cartheur/aiventure-rodney/self-programming/trainer/circuit/CircuitDesc.md

# Creating a KiCad-Compatible JSON for the 8085 Trainer Schematic

The 8085 trainer kit with 62256 SRAM, 5 MHz clock, and SOD LED can be represented as a JSON schematic for KiCad, describing components and connections for the self-modifying code (program at `0000H`, I/O at `2000H`–`2001H`). While direct drawing isn’t possible, the JSON enables manual schematic entry or scripted import in KiCad.

## Approach
- **JSON**: Lists components (8085, 62256, etc.), pins, and nets.
- **KiCad**: Manually place components and connect nets in `eeschema`, or use a script for netlist import.
- **Assumptions**: Standard KiCad libraries (`device`, `74xx`, `microcontroller`), DIP footprints, no serial interface.
- **Limitations**: JSON is netlist-like, requiring manual placement or scripting for `.kicad_sch`.

## JSON Structure
Provided a JSON with:
- **Components**: 8085A, 62256, 74LS373, 74LS138, 5 MHz crystal, capacitors, resistors, LED, switches, 7805.
- **Nets**: VCC, GND, AD0–AD7, A0–A15, ALE, RD, WR, IO/M, CS_RAM, SOD, etc.
- **Notes**: Decoding, unused pins, KiCad import instructions.

## How to Use in KiCad
1. **Setup**: Install KiCad 7+, create project (`8085_trainer`).
2. **Add Components**: Place 8085A (DIP-40), 62256 (DIP-28), 74LS373, 74LS138, crystal, etc., from JSON.
3. **Connect Nets**: Wire per JSON (e.g., `AD0`: `U1.12` to `U3.3`, `U2.11`). Add VCC/GND power flags.
4. **Decoding**: 74LS138 Y0 to 62256 CS (`0000H`–`7FFFH`). G1 to IO/M, G2A/G2B to ground.
5. **Input**: DIP switch to 62256 D0–D7 for `2000H`.
6. **Annotate/Check**: Run `Annotate Schematic`, ERC.
7. **PCB**: Assign footprints, generate netlist, route in `pcbnew`.
8. **Manual Adjustments**: Use generic DIP-40 for 8085 if no symbol, add annotations.

## Loading JSON
- **Manual**: Place components, draw nets per JSON in `eeschema`.
- **Netlist**: Convert JSON to `.net` using Python (`skidl`, `kicad-netlist-utils`), import via `Tools > Import Netlist`.
- **Verify**: Check nets (e.g., `ALE`, `CS_RAM`), run ERC.

## Alternative: Manual Drawing
- **Components**: Place 8085, 62256, 74LS373, 74LS138, 5 MHz crystal, capacitors (22 pF, 10 µF, 0.1 µF, 100 µF), resistors (10 kΩ, 330Ω), LED, push-button, DIP switch, 7805.
- **Wiring**:
  - 8085: VCC, VSS, 5 MHz crystal, reset, SOD to LED.
  - 74LS373: Demultiplex AD0–AD7 to A0–A7.
  - 62256: A0–A14, D0–D7, CS, OE, WE.
  - 74LS138: A13–A15, IO/M, Y0 to CS.
  - DIP switch: To D0–D7.
  - 7805: 5V output, capacitors.
- **Save**: As `8085_trainer.kicad_sch`.

## Notes
- **JSON**: Netlist-like, lacks coordinates/UUIDs. Manual entry simplest.
- **Code**: Supports `0000H`, `2000H`–`2001H`, SOD LED.
- **62256**: A13–A14 grounded (8 KB) or decoded (32 KB).
- **5 MHz**: Compatible, no code changes.
- **KiCad**: Use global labels, group components, run ERC.

## Next Steps
- Enter schematic manually or script JSON to `.kicad_sch`.
- Export to PCB, build circuit.
- Test 62256, 5 MHz, SOD LED, `2001H` output.
- Document with PDF schematic, JSON, `selfmod.lst`.
