cartheur/aiventure-rodney/errata/Trainer-8085-schematic.odt

The circuit schematic for the 8085 trainer kit

Creating a schematic for the 8085 trainer kit with a 62256 SRAM, 5 MHz clock, and SOD LED indicator, as described, is feasible for visualization or implementation in KiCad. While I cannot directly draw a schematic (as I lack graphical output), I can provide a detailed JSON-like structure representing the schematic’s components, connections, and netlist, which you can import into KiCad to generate a schematic. This JSON will describe the 8085, 62256 SRAM, 74LS373 latch, 74LS138 decoder, 5 MHz clock circuit, reset circuit, SOD LED, DIP switch for input, and power supply, tailored to the self-modifying code’s requirements (program at 0000H, I/O at 2000H–2001H).

Approach

- JSON Structure: I’ll define a JSON object that includes:
  - Components (e.g., 8085, 62256, etc.) with part numbers, footprints, and pin assignments.
  - Nets (connections between pins, e.g., 8085 AD0–AD7 to 74LS373 D0–D7).
  - Annotations for KiCad compatibility (e.g., library references, net names).
- KiCad Import: You can use this JSON as a reference to manually create the schematic in KiCad or convert it to a KiCad schematic file (.kicad_sch) using a script (e.g., Python with kicad-netlist-utils) or a netlist import tool. KiCad’s native schematic format is complex, so the JSON will focus on a netlist-like structure that you can adapt.
- Assumptions:
  - Standard KiCad libraries (device, 74xx, microcontroller) are available.
  - Footprints assume DIP packages (e.g., DIP-40 for 8085, DIP-28 for 62256).
  - No serial interface (MAX232) is included to simplify the design, as the code can be loaded manually or via a monitor program.
- Limitations:
  - KiCad’s JSON import is not native for schematics; you’ll need to manually place components and route nets based on the JSON or use a netlist converter.
  - I’ll provide a simplified JSON for clarity, focusing on key connections. You may need to adjust for KiCad’s exact schema (e.g., UUIDs, coordinates).

JSON Schematic Representation

Below is a JSON-like structure describing the 8085 trainer kit’s schematic. It includes components, their pins, and net connections, organized to facilitate KiCad entry. The structure is inspired by netlist formats and KiCad’s schematic requirements.

See “circuit.json” in the repo.

How to Use the JSON in KiCad

1. Set Up KiCad:
  - Install KiCad (version 7 or later recommended).
  - Ensure standard libraries (device, 74xx, microcontroller, memory) are loaded.
  - Create a new project (e.g., 8085_trainer).
2. Create Schematic:
  - Open the Schematic Editor (eeschema).
  - Manually add components based on the JSON’s components section:
    - U1: 8085A (search for 8085 or use a generic DIP-40 microcontroller).
    - U2: HM62256 (use generic SRAM, DIP-28, e.g., 62256 in memory).
    - U3: 74LS373 (in 74xx library).
    - U4: 74LS138 (in 74xx).
    - Y1: Crystal (HC-49 in device).
    - C1–C5: Capacitors (C_0805 or C_1206 in device).
    - R1–R3: Resistors (R_0805 in device).
    - LED1: LED (LED_0805 in device).
    - SW1: Push-button switch (SW_Push in device).
    - SW2: 8-bit DIP switch (DIP-8 in device).
    - U5: 7805 (TO-220 in device).
  - Assign footprints as specified (e.g., DIP-40, DIP-28).
3. Connect Nets:
  - Use the JSON’s nets section to wire components:
    - Example: Net AD0 connects U1.12 (8085 AD0), U3.3 (74LS373 D0), U2.11 (62256 D0).
    - Use KiCad’s wire tool to draw connections.
    - Add labels (e.g., VCC, GND, AD0) for clarity.
  - Add power flags (PWR_FLAG in device) to VCC and GND nets to satisfy ERC (Electrical Rules Check).
  - Ground unused pins as noted (e.g., U1 SID, RST5.5, etc.).
4. Handle Decoding:
  - The 74LS138 selects the 62256 for 0000H–7FFFH (A15=0). Connect U4.6 (G1) to U1.34 (IO/M) directly or via a 74LS04 inverter if IO/M needs inversion.
  - Tie U4.4 (G2A) and U4.5 (G2B) to ground.
  - Connect U4.15 (Y0) to U2.20 (62256 CS).
5. Input Configuration:
  - The DIP switch (SW2) connects to the data bus (D0–D7) for input at 2000H. In KiCad, draw SW2 outputs to U2.11–U2.19 (62256 D0–D7).
  - For simplicity, the code assumes 2000H is RAM; no separate I/O chip is needed. If you want a dedicated input port, add a 74LS244 buffer enabled by a 74LS138 output (e.g., Y1 for 2000H).
6. Annotate and Check:
  - Run Annotate Schematic to assign unique references (e.g., U1, U2).
  - Run ERC to check for unconnected pins or net errors.
  - Manually verify nets against the JSON (e.g., AD0–AD7, A0–A14).
7. Export to PCB (Optional):
  - Assign footprints in eeschema.
  - Run Netlist Generation and import into pcbnew.
  - Place components and route traces for a physical board.
8. Manual Adjustments:
  - If KiCad lacks an 8085 symbol, use a generic DIP-40 microcontroller and label pins per the JSON.
  - Add text annotations in KiCad for clarity (e.g., “62256 CS for 0000H–7FFFH”).
  - If you want a native .kicad_sch file, use a Python script (e.g., kicad-netlist-utils) to convert the JSON to KiCad format, or manually draw based on the JSON.

Steps to Load JSON into KiCad

Since KiCad doesn’t directly import JSON schematics, follow these steps:

1. Manual Entry:
  - Open eeschema and place components listed in components (e.g., 8085A, HM62256).
  - Use the nets section to draw wires (e.g., connect U1.12 to U3.3 for AD0).
  - Label nets (e.g., VCC, GND, A0) for readability.
2. Netlist Conversion (Advanced):
  - Convert the JSON to a KiCad netlist (.net) using a Python script:
    - Parse components and nets to generate a netlist in KiCad’s format (e.g., (net VCC (node U1 40) (node U2 28) ...)).
    - Libraries like skidl or kicad-netlist-utils can help.
  - Import the netlist into eeschema via Tools > Import Netlist.
  - Manually place components, as netlists don’t include coordinates.
3. Verify:
  - Check connections against the JSON (e.g., ALE from U1.30 to U3.11).
  - Run ERC to ensure no floating pins or duplicate nets.
  - Add power flags for VCC and GND.

Alternative: Drawing the Schematic

If you prefer to draw the schematic directly in KiCad without JSON:

1. Add Components:
  - Place the 8085 (DIP-40), 62256 (DIP-28), 74LS373 (DIP-20), 74LS138 (DIP-16), 5 MHz crystal, capacitors (22 pF, 10 µF, 0.1 µF, 100 µF), resistors (10 kΩ, 330Ω), LED, push-button, DIP switch, and 7805.
2. Wire Connections:
  - 8085:
    - Vcc (pin 40), Vss (pin 20), 0.1 µF capacitor.
    - 5 MHz crystal to X1/X2 (pins 1–2), 22 pF capacitors to ground.
    - Reset: 10 µF to 5V, 10 kΩ to ground, push-button across capacitor at RESET_IN (pin 36).
    - SOD (pin 4) to 330Ω resistor, to LED cathode, anode to 5V.
    - Ground TRAP (pin 6) via 10 kΩ.
  - 74LS373:
    - D0–D7 (pins 3, 4, 7, 8, 13, 14, 17, 18) to 8085 AD0–AD7 (pins 12–19).
    - Q0–Q7 (pins 2, 5, 6, 9, 12, 15, 16, 19) to 62256 A0–A7 (pins 10, 9, 8, 7, 6, 5, 4, 3).
    - G (pin 11) to 8085 ALE (pin 30), OC (pin 1) to ground.
  - 62256:
    - A0–A12 (pins 10, 9, 8, 7, 6, 5, 4, 3, 25, 24, 21, 23, 2) to A0–A12 (A0–A7 from 74LS373, A8–A12 from 8085 pins 21–25).
    - A13–A14 (pins 26, 1) to 8085 A13–A14 (pins 26–27) or ground for 8 KB.
    - D0–D7 (pins 11–13, 15–19) to 8085 AD0–AD7.
    - CS (pin 20) to 74LS138 Y0 (pin 15).
    - OE (pin 22) to 8085 RD (pin 32), WE (pin 27) to WR (pin 31).
  - 74LS138:
    - A, B, C (pins 1–3) to 8085 A13–A15 (pins 26–28).
    - G1 (pin 6) to 8085 IO/M (pin 34), G2A/G2B (pins 4–5) to ground.
    - Y0 (pin 15) to 62256 CS.
  - DIP Switch:
    - Outputs (D0–D7) to 62256 D0–D7 (pins 11–13, 15–19) via 10 kΩ pull-ups to 5V.
    - Enable via 74LS138 Y1 (pin 14) for 2000H read (optional; code uses RAM).
  - Power:
    - 7805 VOUT (pin 3) to VCC net, VIN (pin 1) to 9–12V, GND (pin 2).
    - 100 µF, 0.1 µF capacitors at 7805 input/output.
3. Annotate and Save:
  - Run Annotate Schematic.
  - Save as 8085_trainer.kicad_sch.

Notes

- JSON Limitations:
  - The JSON is a netlist-like representation, not a native KiCad .kicad_sch file. It lacks graphical coordinates and UUIDs, requiring manual placement in KiCad.
  - For a true .kicad_sch, you’d need a Python script to generate KiCad’s S-expression format, which is complex and beyond this scope.
- Simplifications:
  - The DIP switch is connected directly to the data bus, assuming 2000H input is set via RAM writes or manual monitor entry. A proper I/O port (e.g., 74LS244) would need additional decoding.
  - No EPROM or serial interface is included to keep the schematic minimal. Add a 2764 or MAX232 if needed.
- KiCad Tips:
  - Use global labels (e.g., VCC, GND) to reduce clutter.
  - Group components logically (e.g., 8085 near 74LS373, 62256 near 74LS138).
  - Save frequently and run ERC to catch errors.
- Code Compatibility:
  - The schematic supports the code’s requirements: program at 0000H, I/O at 2000H–2001H, SOD LED for self-modification.
  - The 62256’s 32 KB covers all addresses; grounding A13–A14 simplifies decoding to 8 KB if preferred.
  - The 5 MHz clock (2.5 MHz internal) is compatible, with no code changes needed.

Next Steps

1. Manual KiCad Entry:
  - Use the JSON as a reference to place components and draw nets in eeschema.
  - Start with the 8085, add 74LS373 for demultiplexing, then 62256 and 74LS138.
  - Add clock, reset, LED, and DIP switch last.
2. Scripted Import (Optional):
  - Write a Python script to convert the JSON to a KiCad netlist or .kicad_sch file.
  - Example libraries: skidl for schematic generation, kicad-python for KiCad file manipulation.
3. PCB Design:
  - After completing the schematic, generate a netlist and import into pcbnew for PCB layout.
  - Use DIP sockets for easy IC replacement.
4. Build and Test:
  - Assemble the circuit on a breadboard or PCB based on the KiCad schematic.
  - Test as described (5 MHz clock, 62256 access, SOD LED, 2001H output).
5. Documentation:
  - Export the KiCad schematic as a PDF for reference.
  - Keep the JSON and selfmod.lst for debugging.
