cartheur/aiventure-rodney/diagrams/RodneyWirewrapStack.pdf

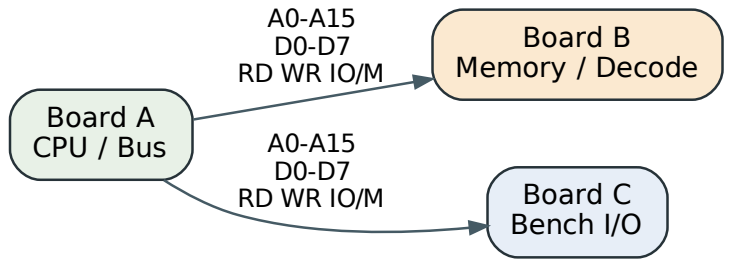
[picture p6: figure]
Board A CPU / Bus; Board B Memory / Decode; Board C Bench I/O
