cartheur/aiventure-rodney/book/figures/Figure-04_1.jpg

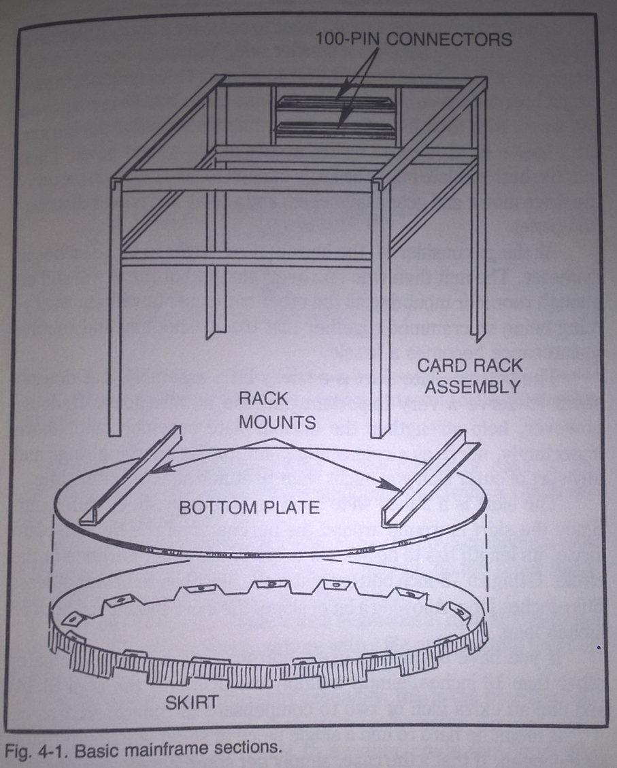
book/figures/Figure-04_1.jpg
