cartheur/aiventure-rodney/book/figures/Figure-04_2.jpg

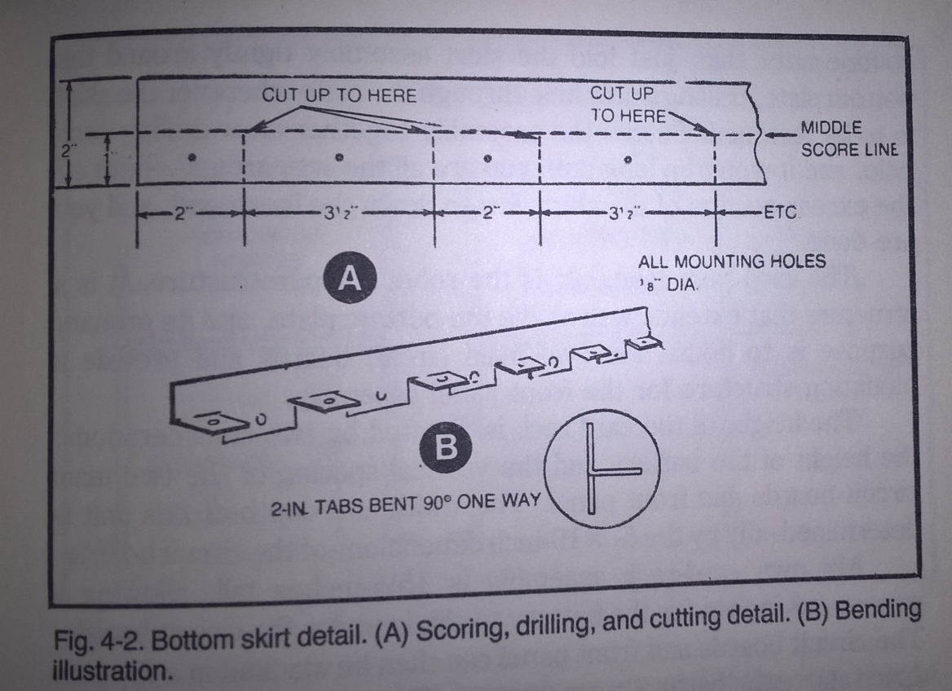
book/figures/Figure-04_2.jpg
