cartheur/aiventure-rodney/book/figures/Figure-04_3.jpg

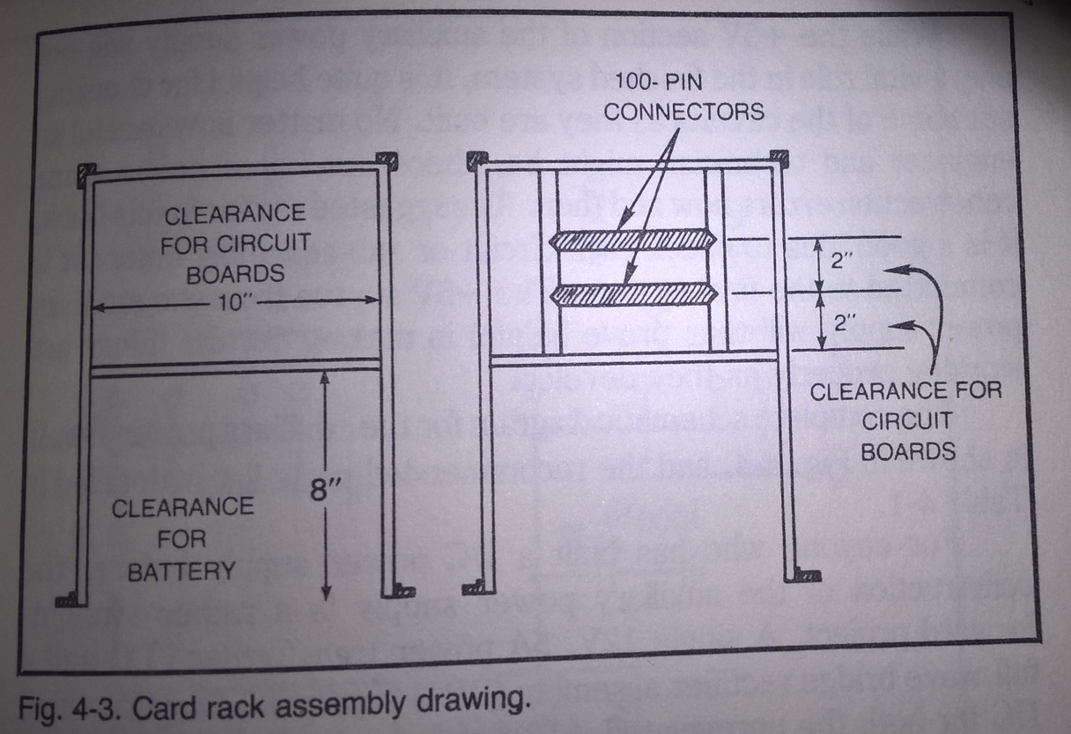
book/figures/Figure-04_3.jpg
