cartheur/aiventure-rodney/book/figures/Figure-04_5.jpg

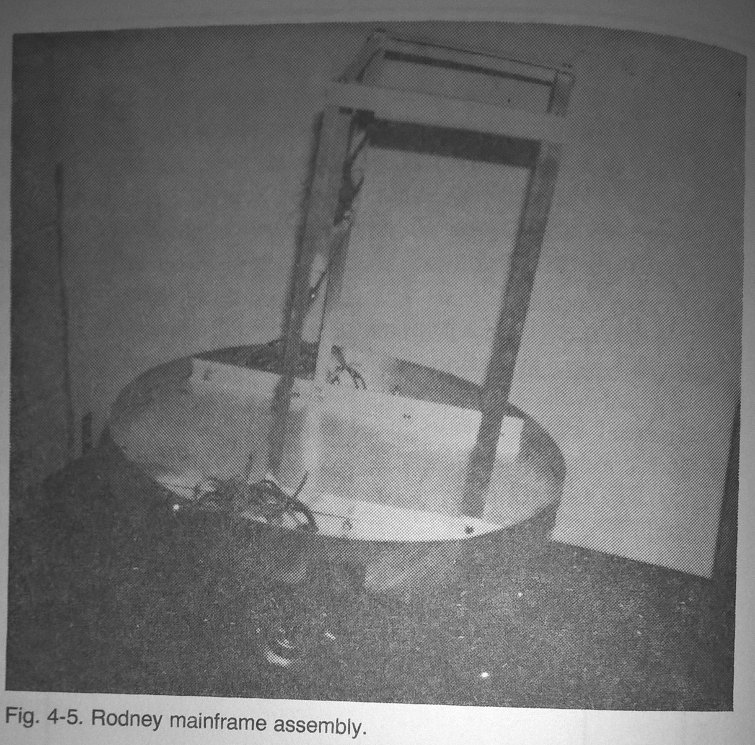
book/figures/Figure-04_5.jpg
