cartheur/aiventure-rodney/book/figures/Figure-05_12.jpg

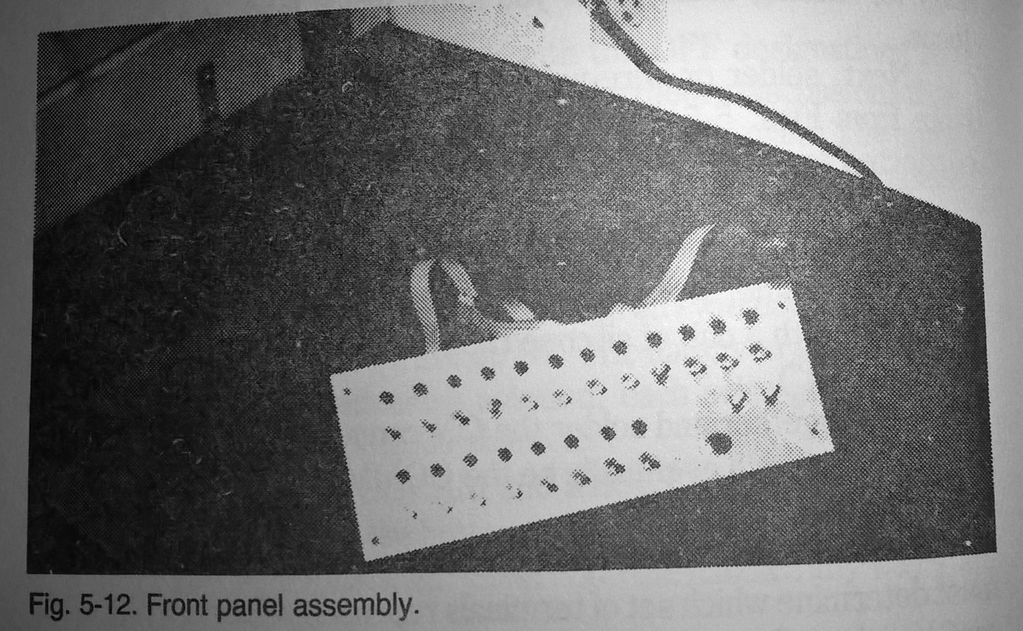
book/figures/Figure-05_12.jpg
