cartheur/aiventure-rodney/book/figures/Figure-06_7.jpg

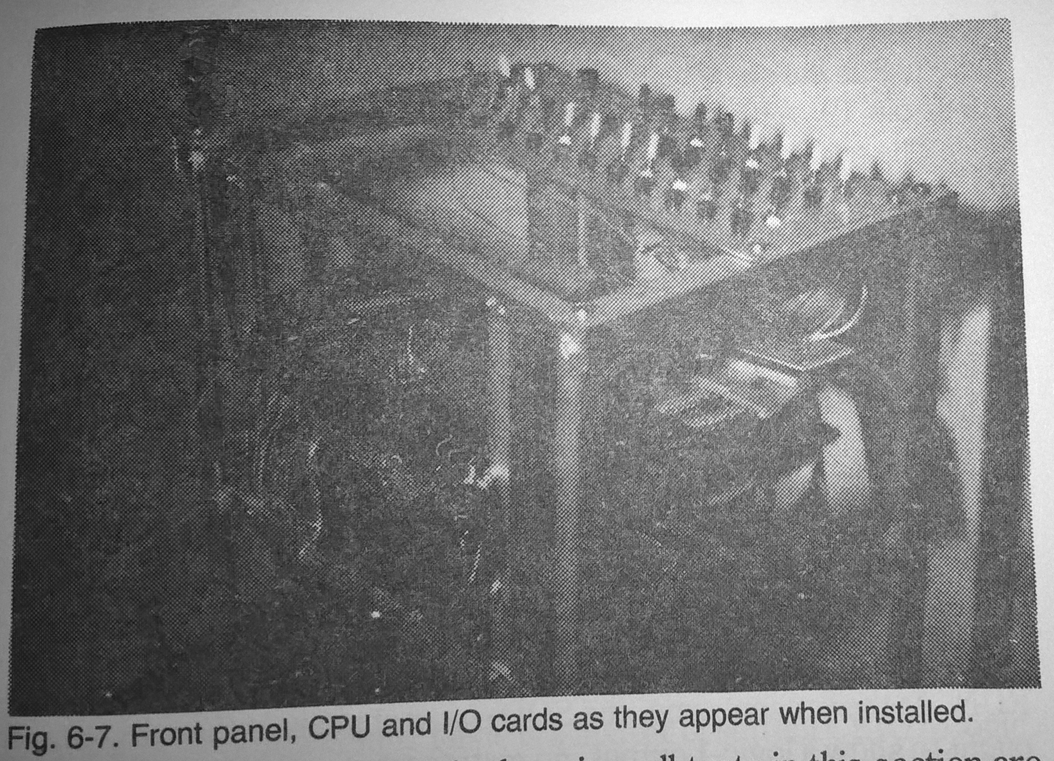
book/figures/Figure-06_7.jpg
