cartheur/aiventure-rodney/book/figures/Figure-07_9.jpg

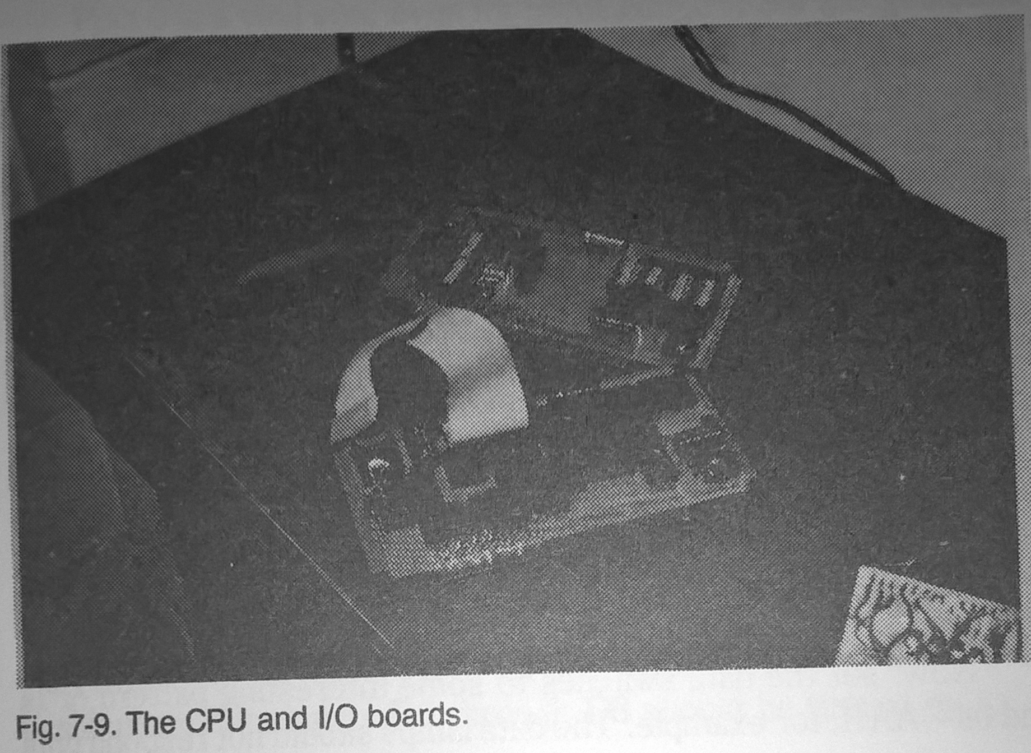
book/figures/Figure-07_9.jpg
