cartheur/aiventure-rodney/book/figures/Figure-08_8.jpg

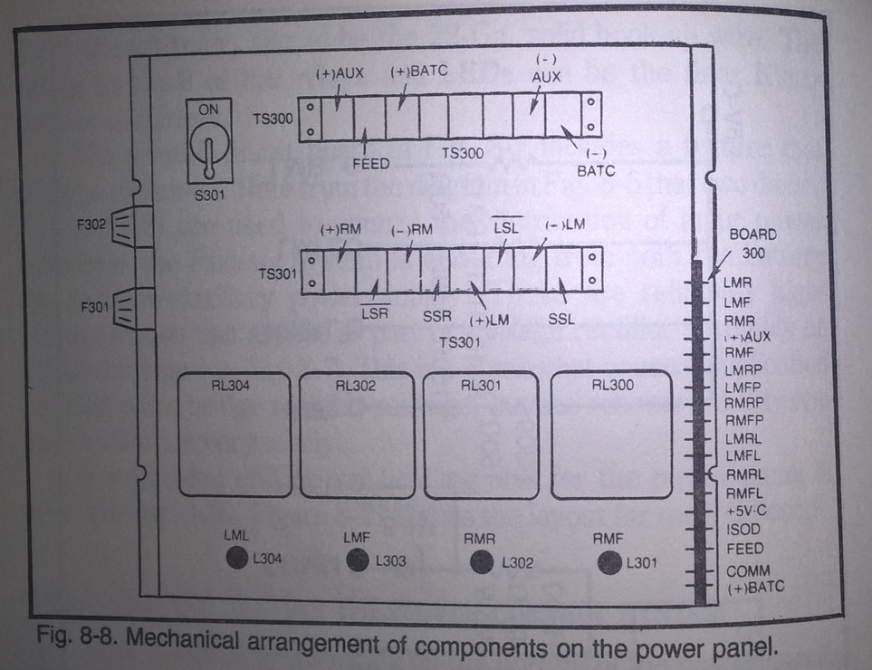
book/figures/Figure-08_8.jpg
