cartheur/aiventure-rodney/book/figures/Figure-08_9.jpg

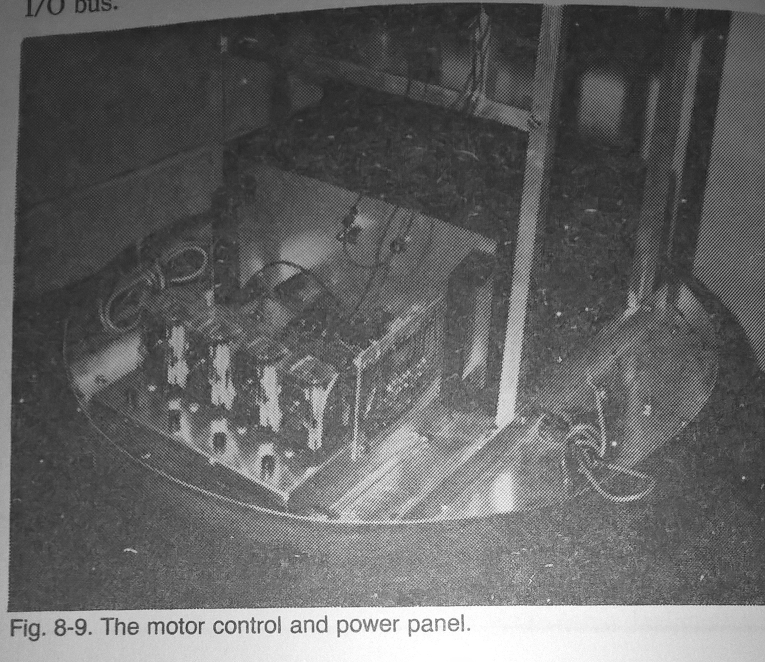
book/figures/Figure-08_9.jpg
