cartheur/aiventure-rodney/book/figures/Figure-08_10.jpg

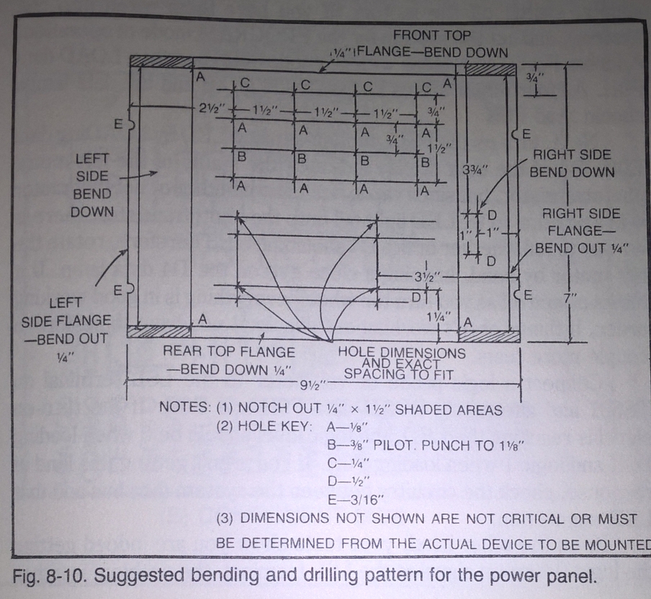
book/figures/Figure-08_10.jpg
