cartheur/aiventure-rodney/book/figures/Figure-08_12.jpg

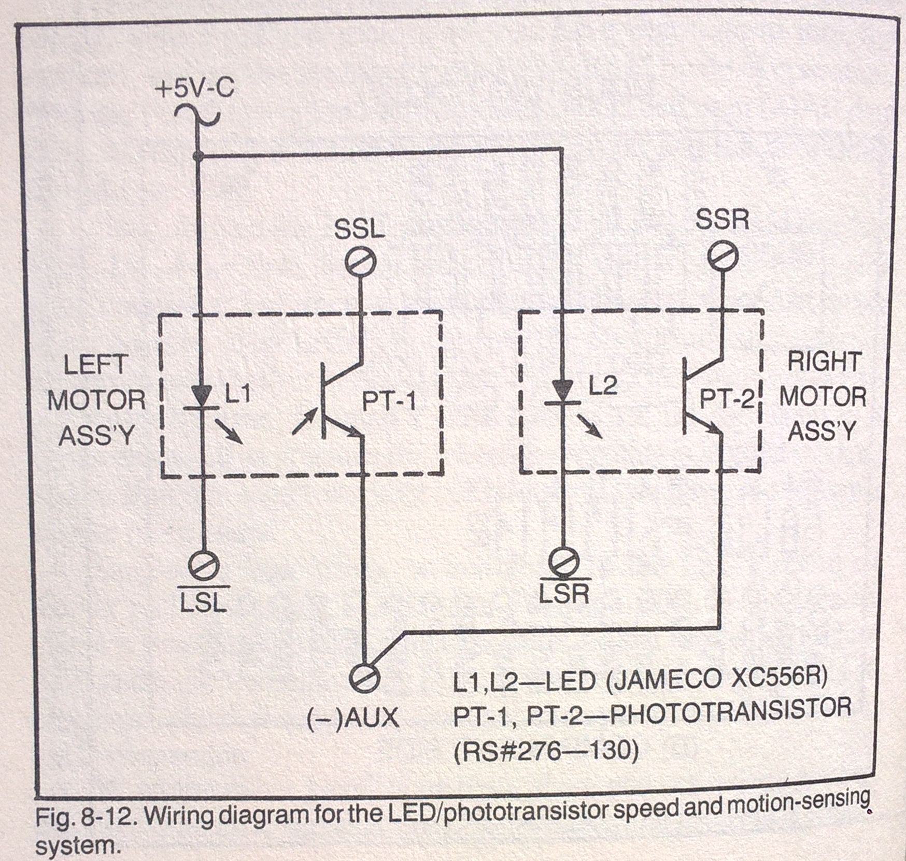
book/figures/Figure-08_12.jpg
