cartheur/aiventure-rodney/book/figures/Figure-08_13.jpg

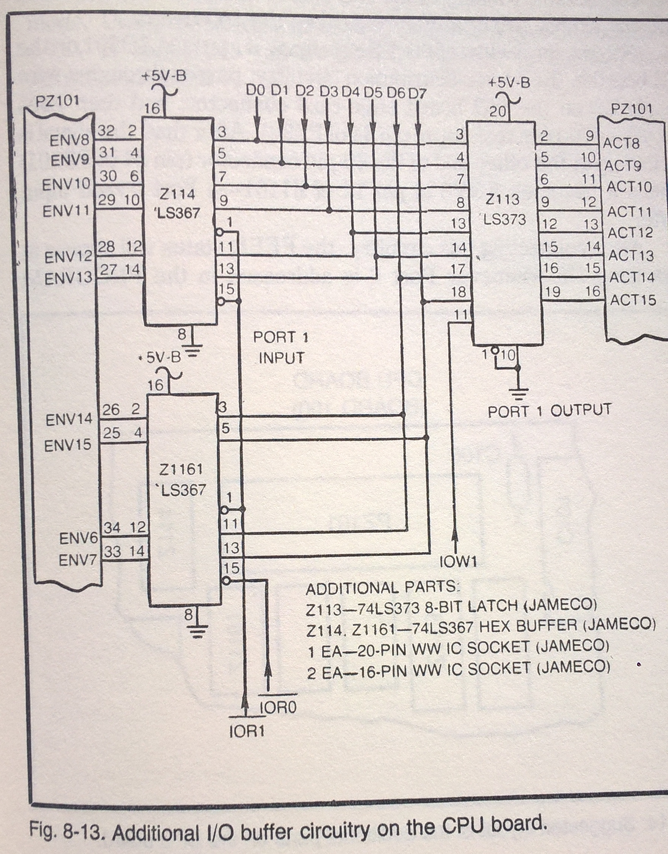
book/figures/Figure-08_13.jpg
