cartheur/aiventure-rodney/book/figures/Figure-09_5.jpg

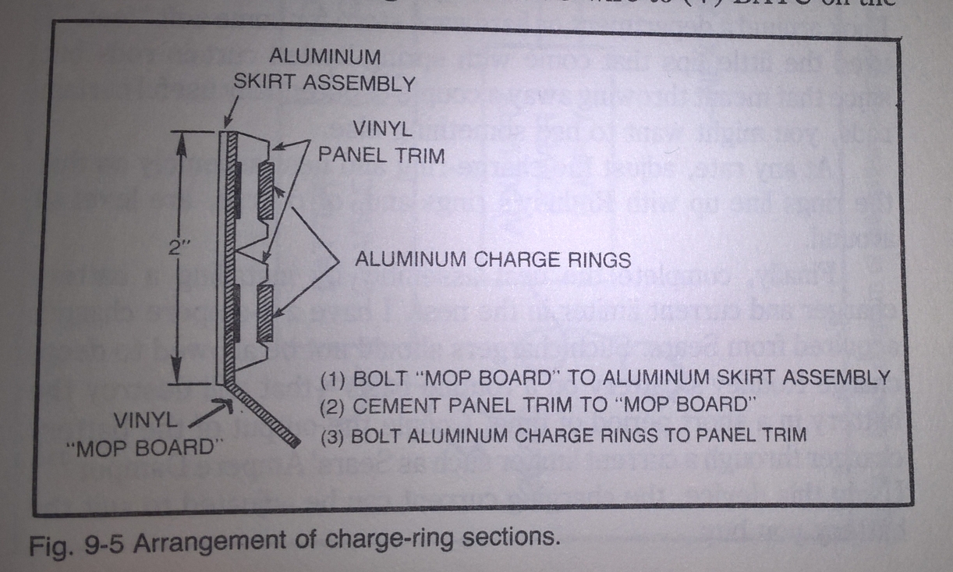
book/figures/Figure-09_5.jpg
