cartheur/aiventure-rodney/book/finished/Rodney-Heiserman-1979-p1a-x640.jpg

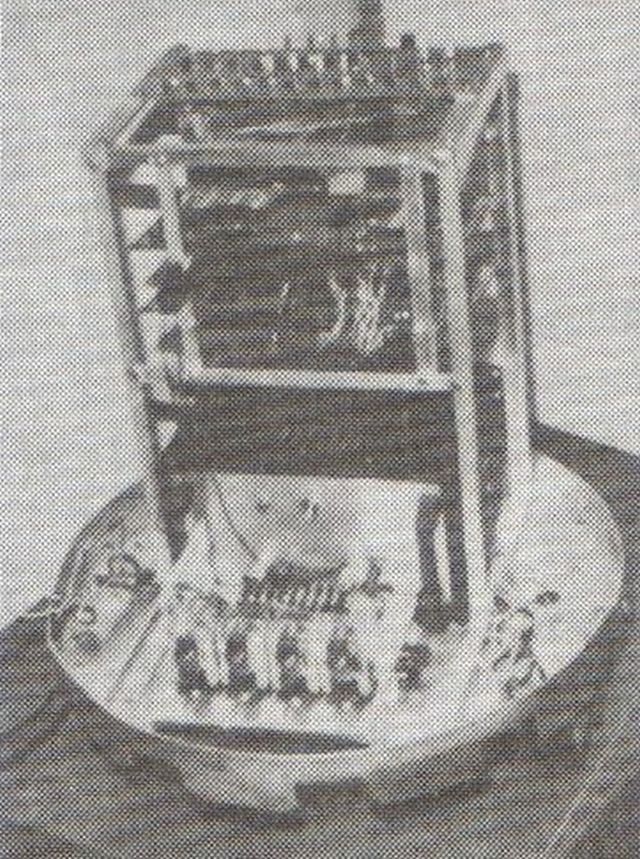
book/finished/Rodney-Heiserman-1979-p1a-x640.jpg
