cartheur/aiventure-rodney/book/finished/Rodney-Heiserman-1979-p1b-x640.jpg

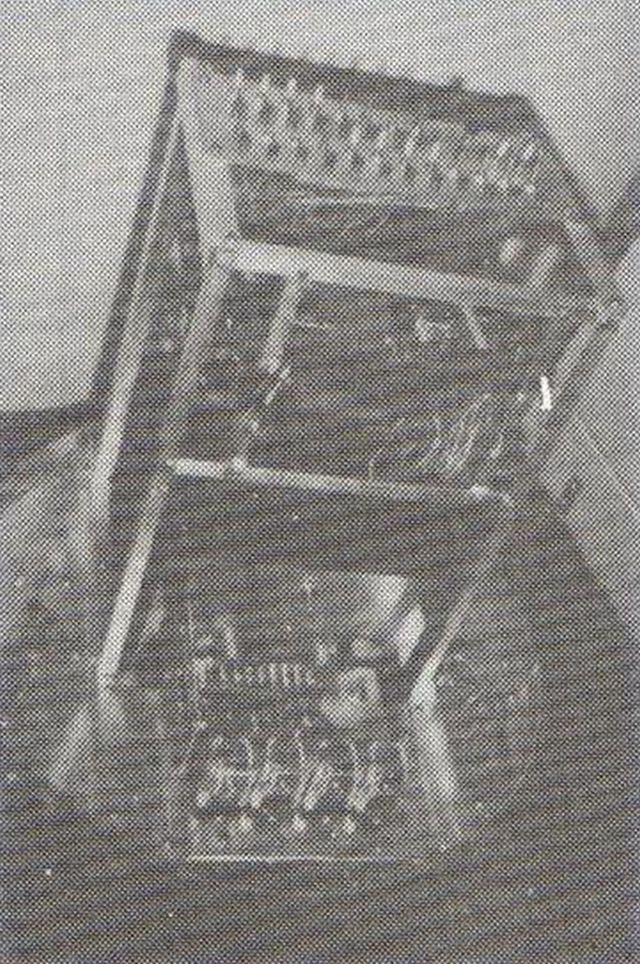
book/finished/Rodney-Heiserman-1979-p1b-x640.jpg
