cartheur/aiventure-rodney/book/finished/Rodney-Heiserman-1979-p2-x640.jpg

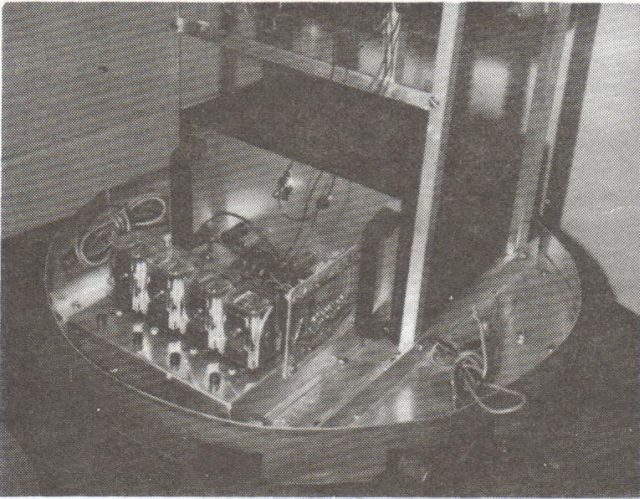
book/finished/Rodney-Heiserman-1979-p2-x640.jpg
