cartheur/aiventure-rodney/book/programming/3.jpg

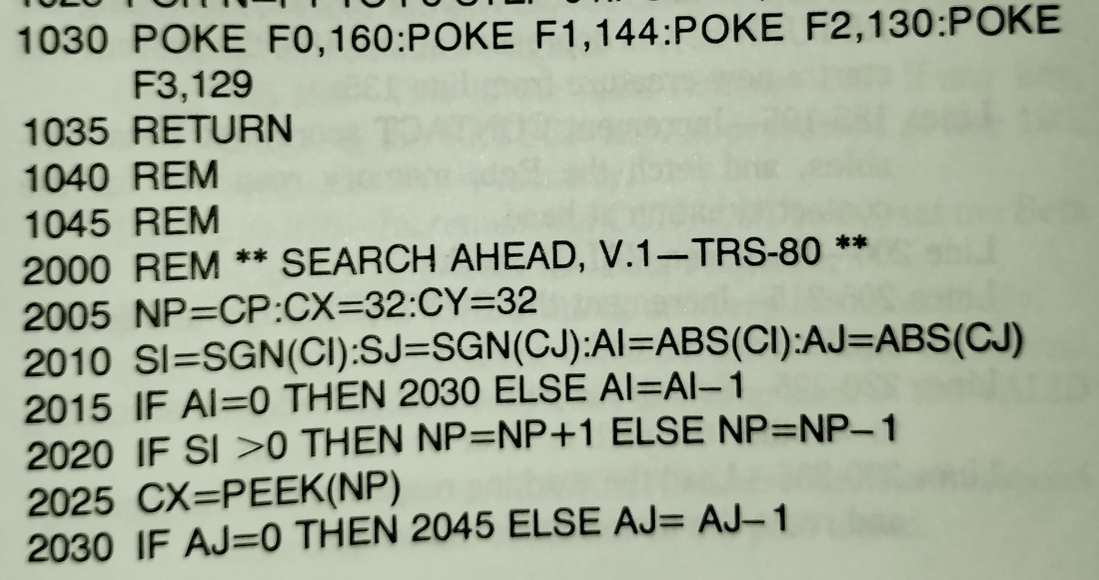
book/programming/3.jpg
