cartheur/aiventure-rodney/book/programming/fig.19-3.jpg

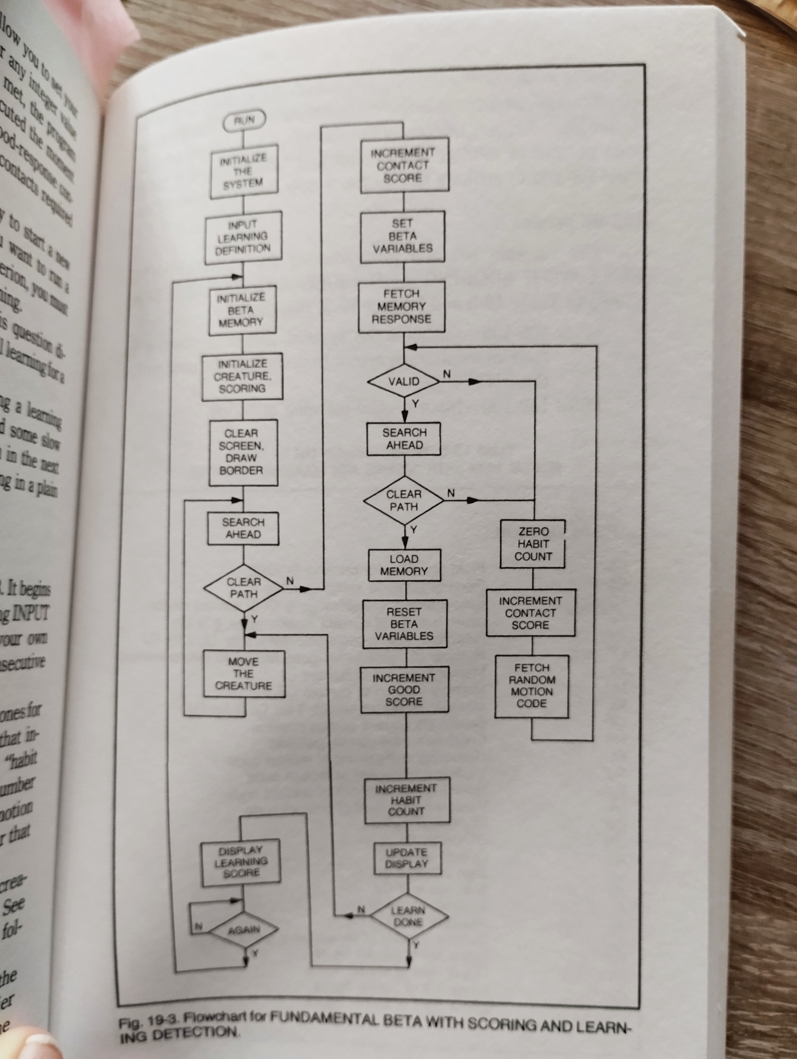
book/programming/fig.19-3.jpg
