cartheur/aiventure-rodney/book/programming/fig.19.2.jpg

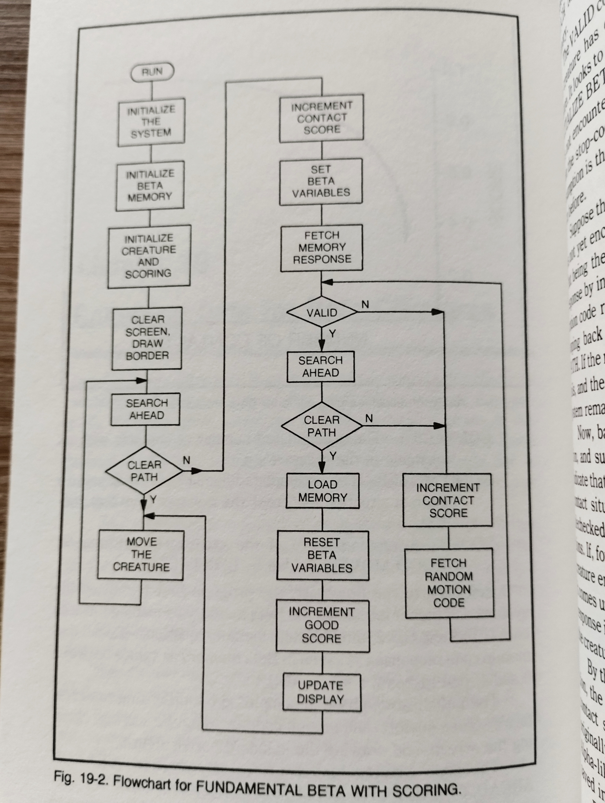
book/programming/fig.19.2.jpg
