cartheur/aiventure-rodney/book/programming/p272.jpg

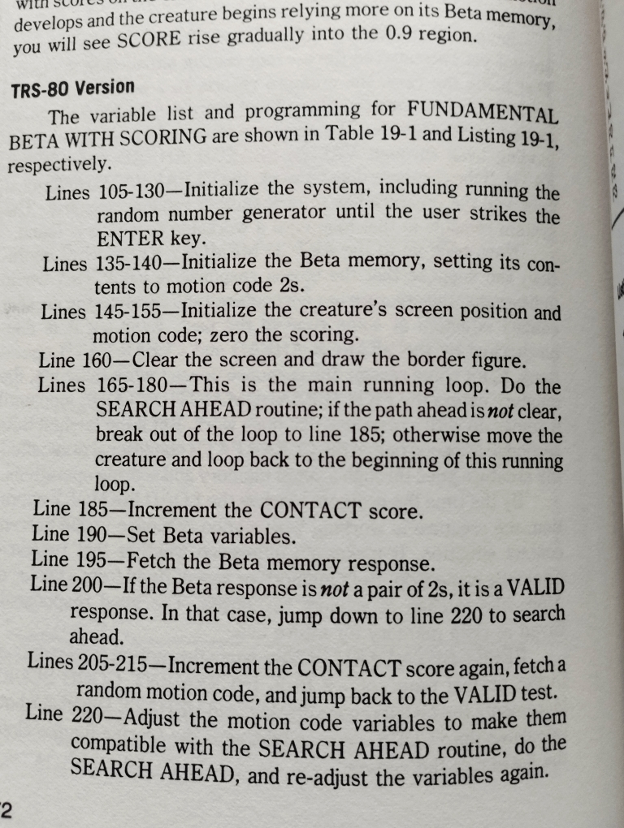
book/programming/p272.jpg
