cartheur/aiventure-rodney/book/tables/Table-04_1.jpg

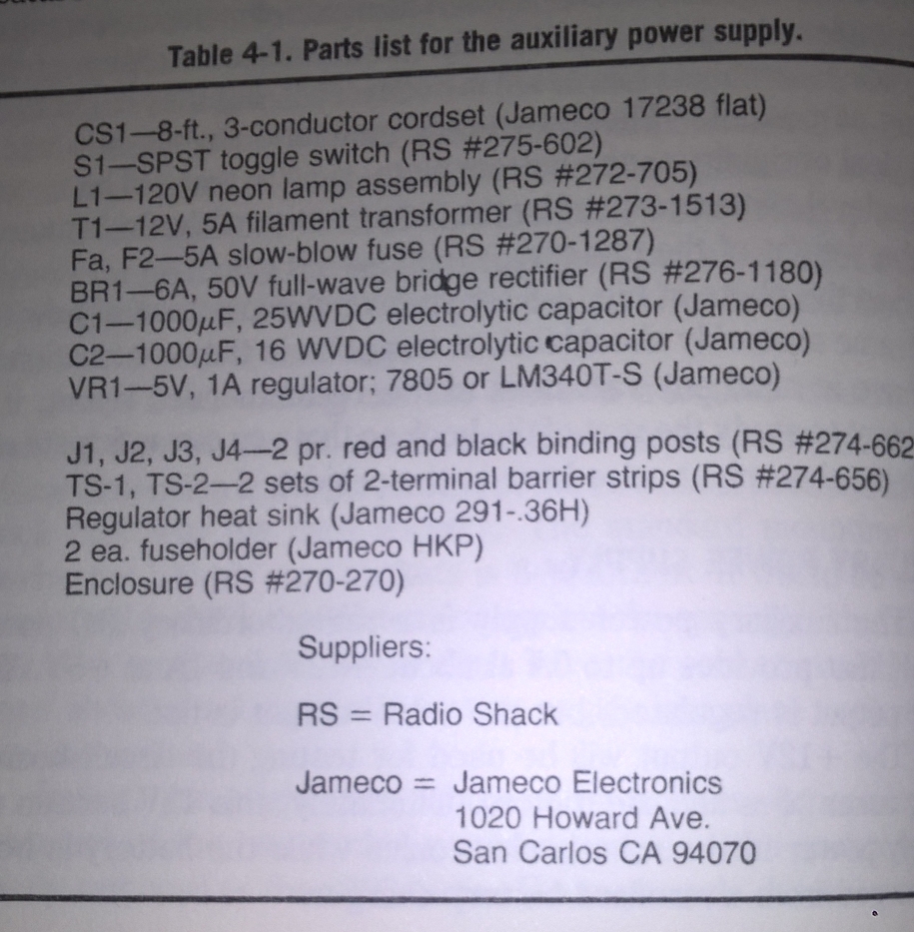
book/tables/Table-04_1.jpg
