cartheur/aiventure-rodney/book/tables/Table-05_1.jpg

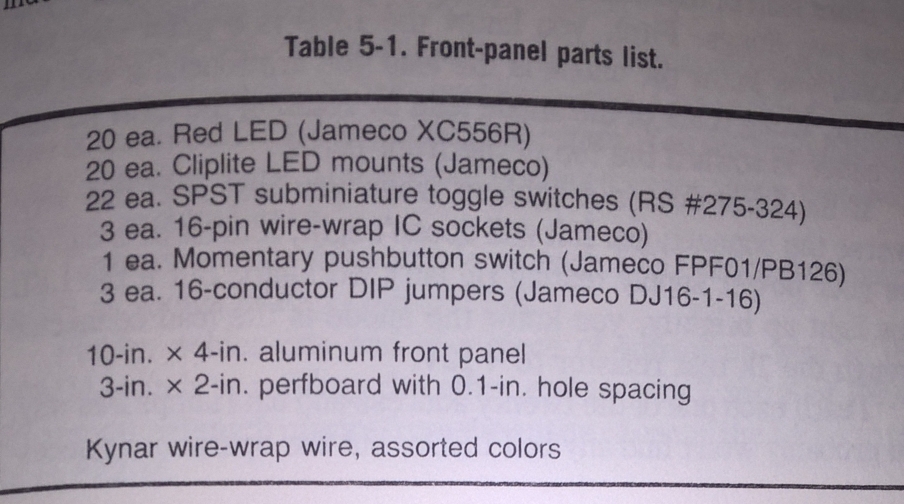
book/tables/Table-05_1.jpg
