cartheur/aiventure-rodney/book/tables/Table-05_2.jpg

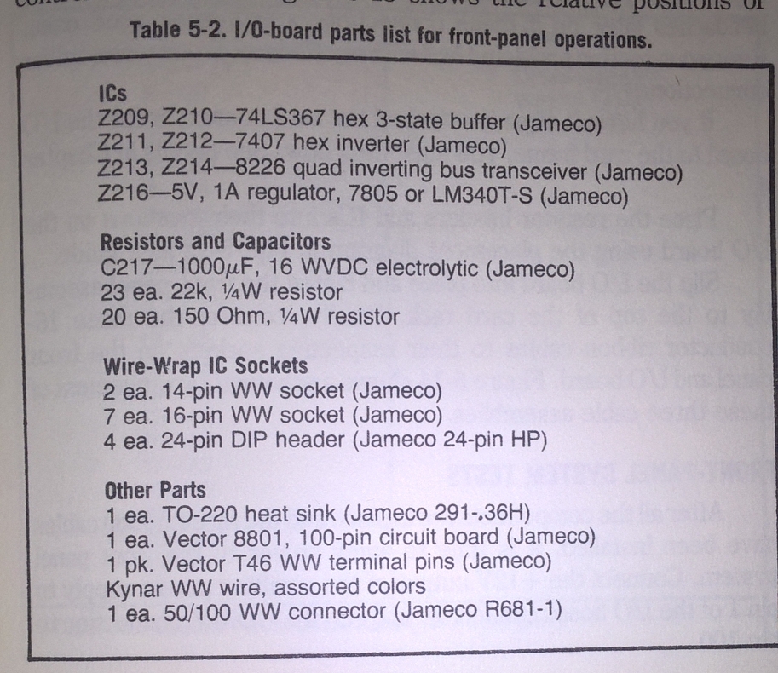
book/tables/Table-05_2.jpg
