cartheur/aiventure-rodney/book/tables/Table-06_3.jpg

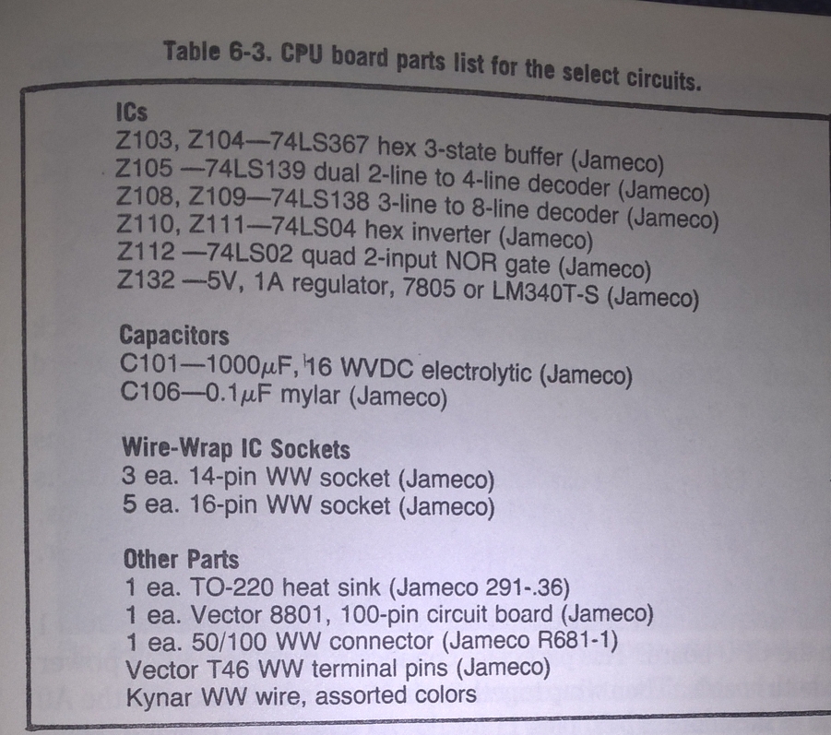
book/tables/Table-06_3.jpg
