cartheur/aiventure-rodney/book/tables/Table-07_2.jpg

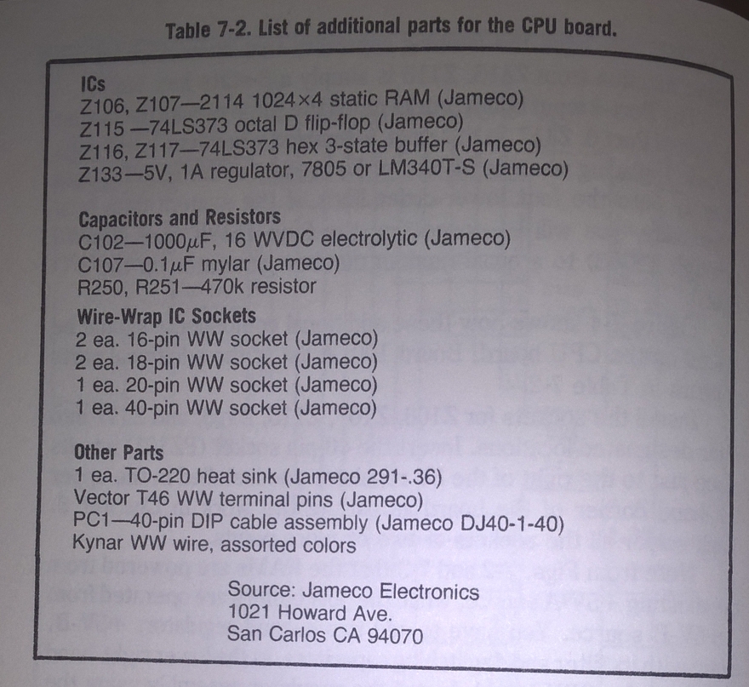
book/tables/Table-07_2.jpg
