cartheur/aiventure-rodney/book/tables/Table-08_2.jpg

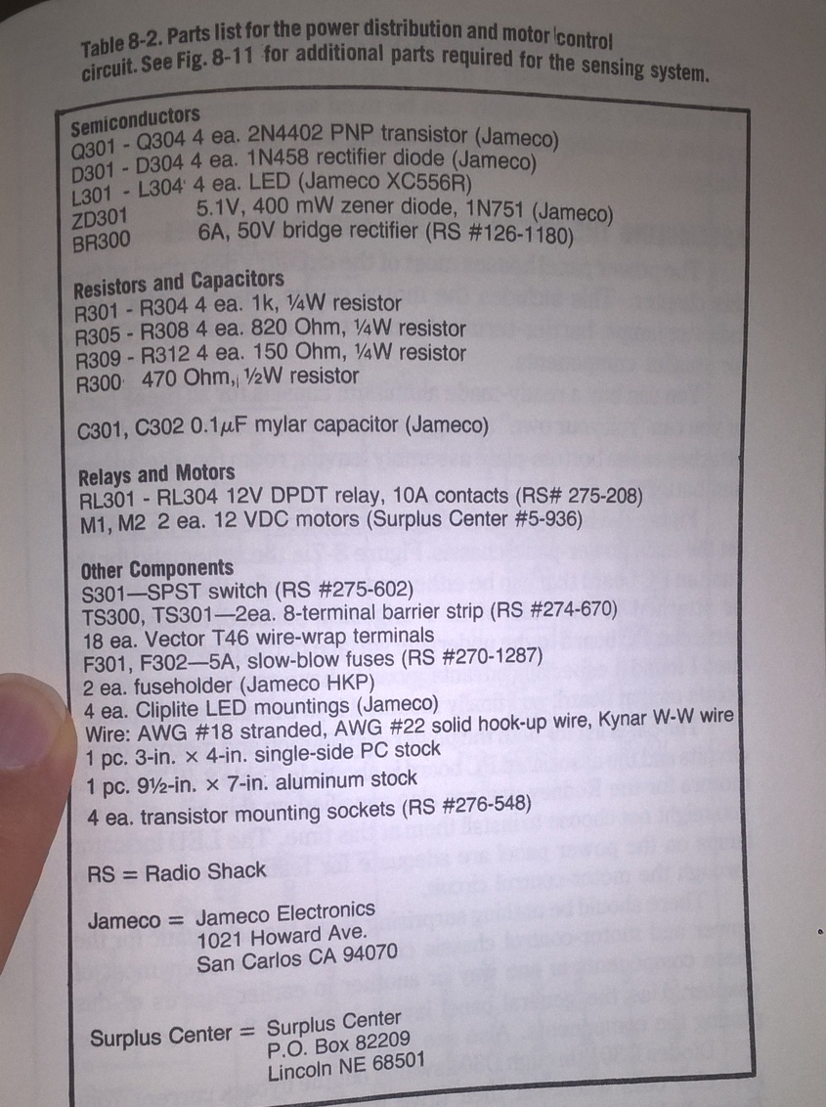
book/tables/Table-08_2.jpg
