cartheur/aiventure-rodney/book/tables/Table-09_1.jpg

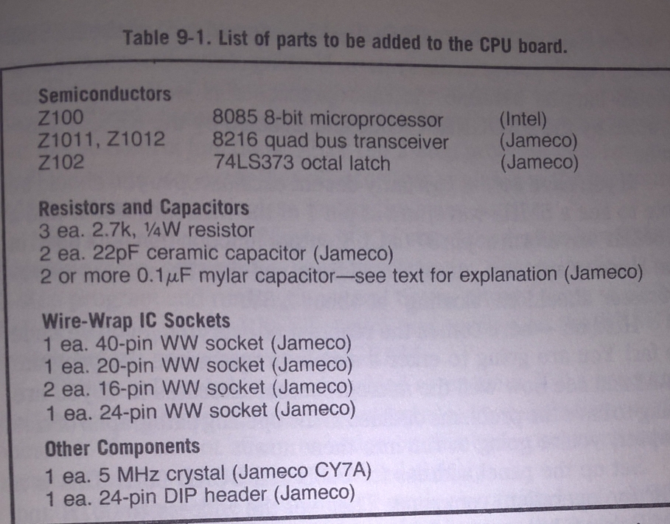
book/tables/Table-09_1.jpg
