cartheur/aiventure-rodney/book/tables/Table-09_2.jpg

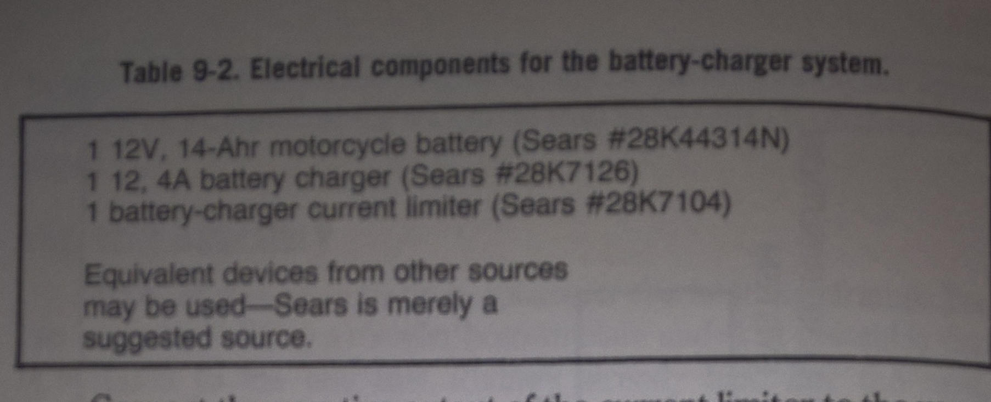
book/tables/Table-09_2.jpg
