cartheur/aiventure-rodney/book/tables/Table-11_1.jpg

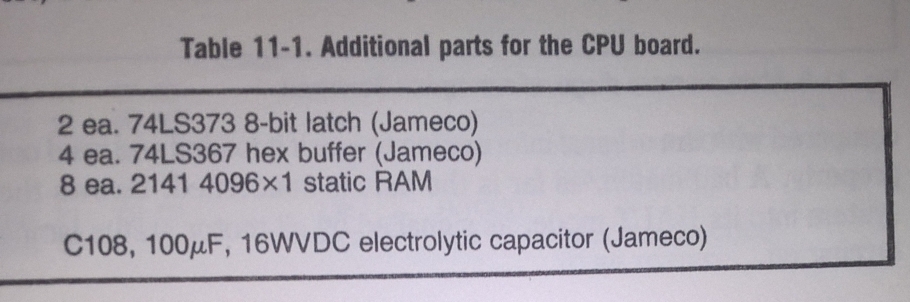
book/tables/Table-11_1.jpg
