cartheur/aiventure-rodney/build-of-materials/datasheets/vector/8801-6-specs.png

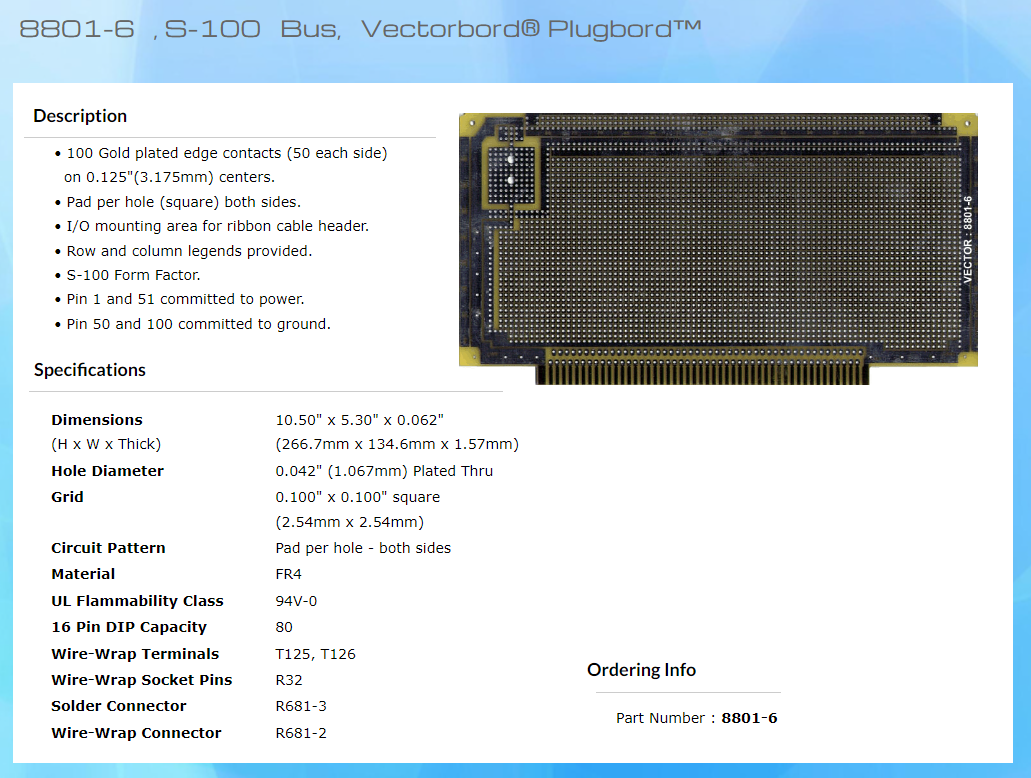
build-of-materials/datasheets/vector/8801-6-specs.png
