cartheur/aiventure-rodney/build/5-front-panel/images/panel_design.png

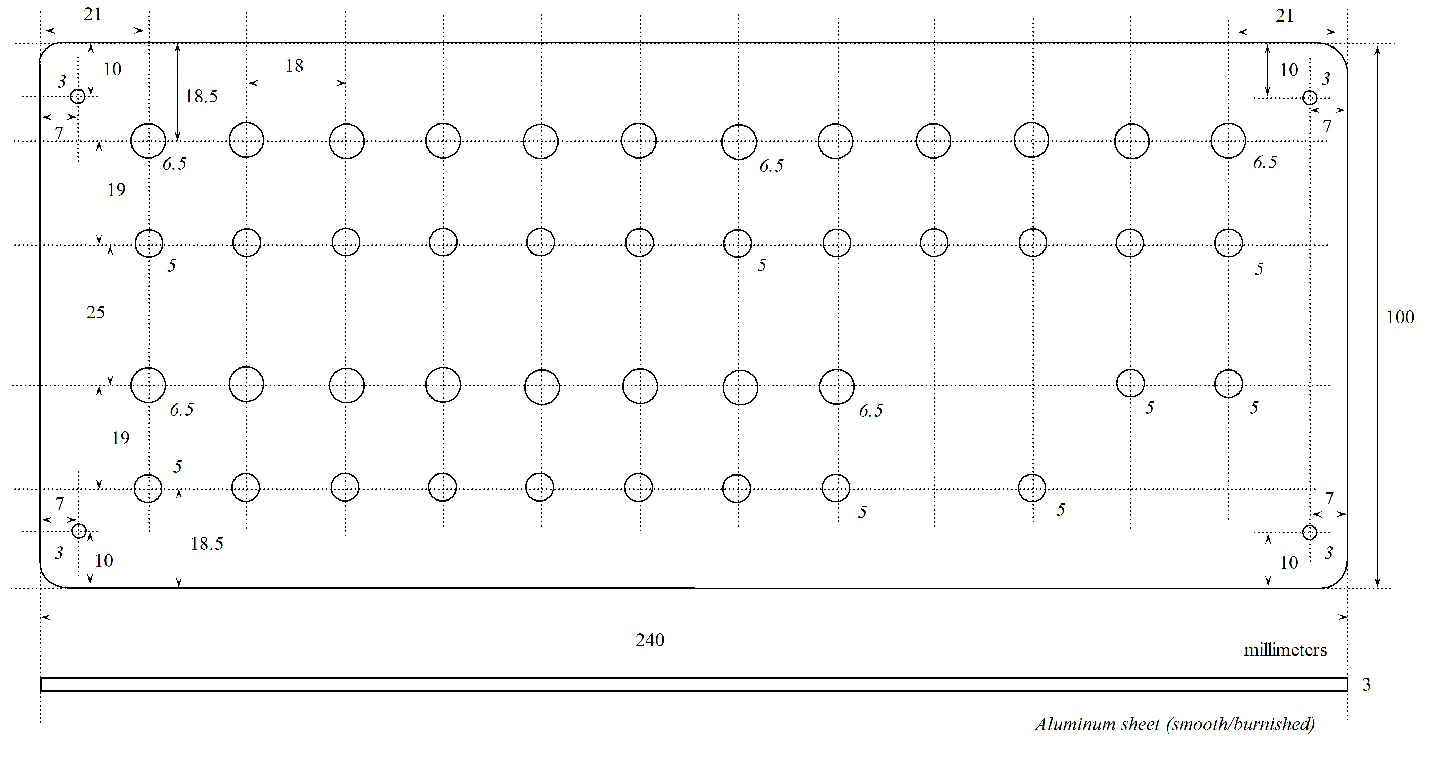
build/5-front-panel/images/panel_design.png
