cartheur/aiventure-rodney/design/rodney-bw.jpg

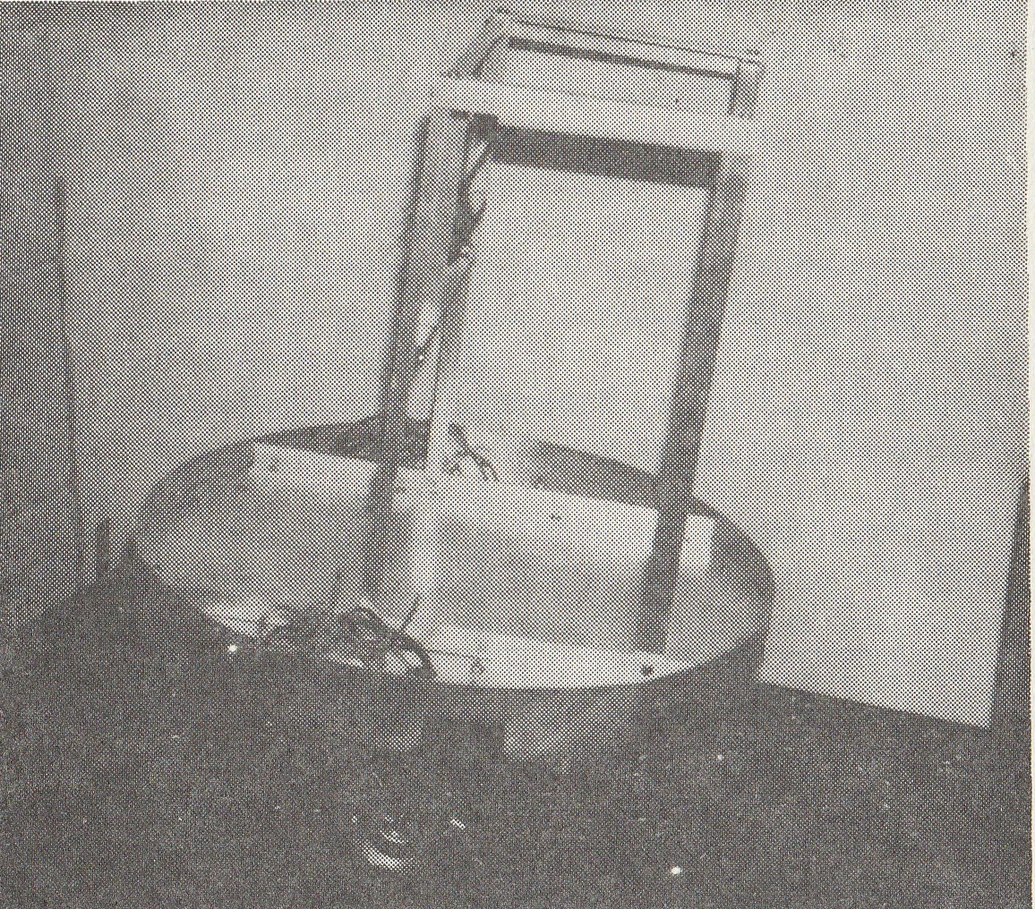
design/rodney-bw.jpg
