cartheur/aiventure-rodney/design/rodney-color.jpg

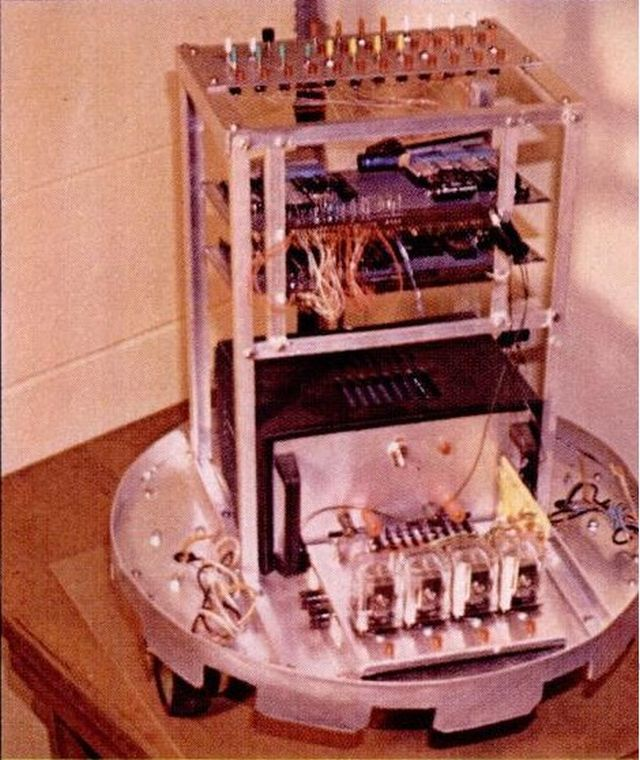
design/rodney-color.jpg
