cartheur/aiventure-rodney/development/prototype/major-tom.jpg

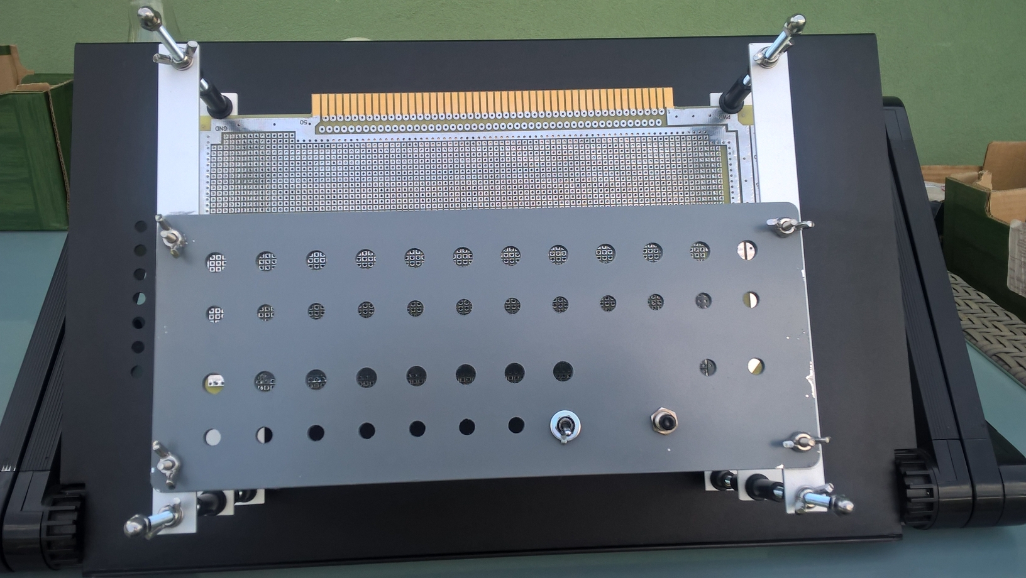
development/prototype/major-tom.jpg
