cartheur/aiventure-rodney/diagrams/EmbodiedBehaviors.jpg

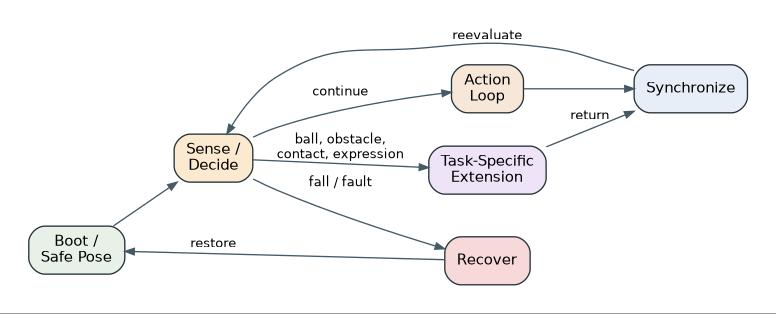
diagrams/EmbodiedBehaviors.jpg
