cartheur/aiventure-rodney/diagrams/RodneyBoardA-silkscreen.jpg

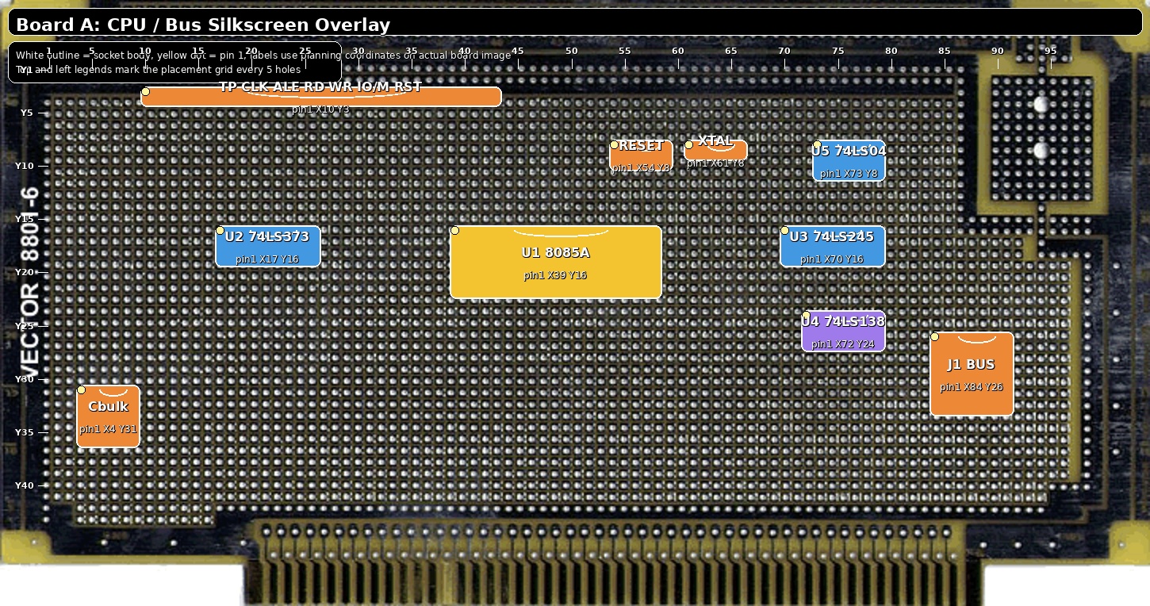
diagrams/RodneyBoardA-silkscreen.jpg
