cartheur/aiventure-rodney/diagrams/RodneyBoardA-worksheet.jpg

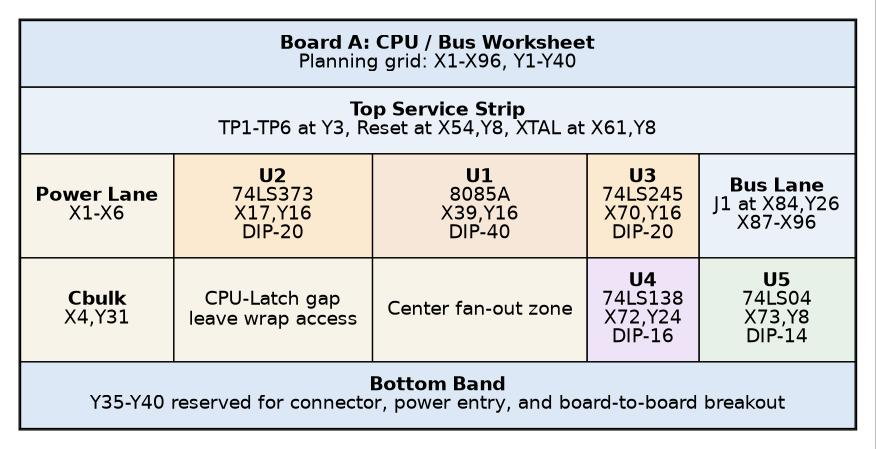
diagrams/RodneyBoardA-worksheet.jpg
