cartheur/aiventure-rodney/diagrams/RodneyBoardA.jpg

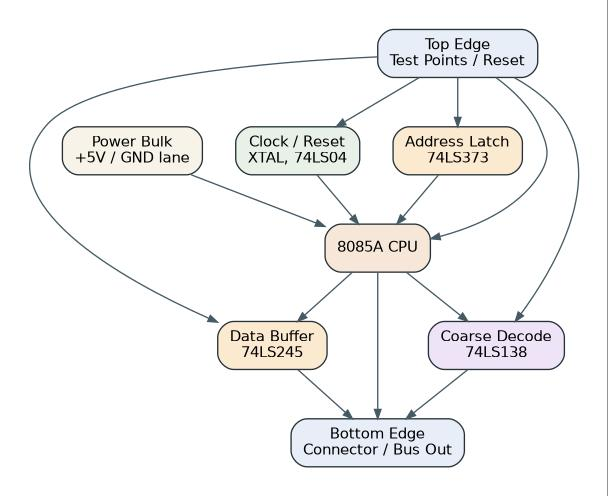
diagrams/RodneyBoardA.jpg
