cartheur/aiventure-rodney/diagrams/RodneyBoardB-silkscreen.jpg

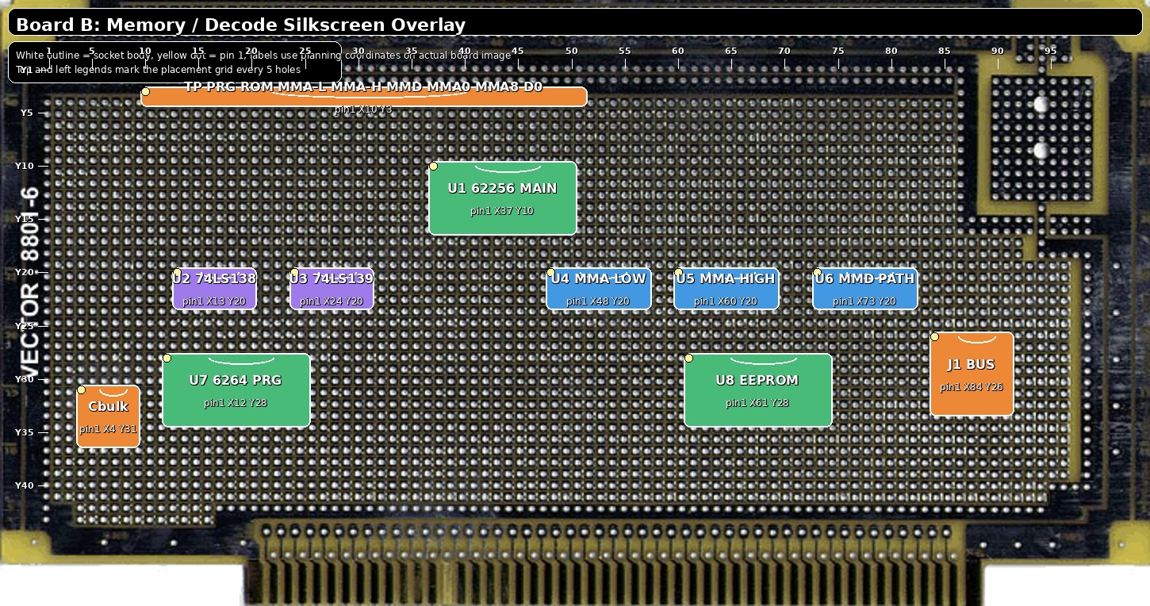
diagrams/RodneyBoardB-silkscreen.jpg
