cartheur/aiventure-rodney/diagrams/RodneyBoardB-worksheet.jpg

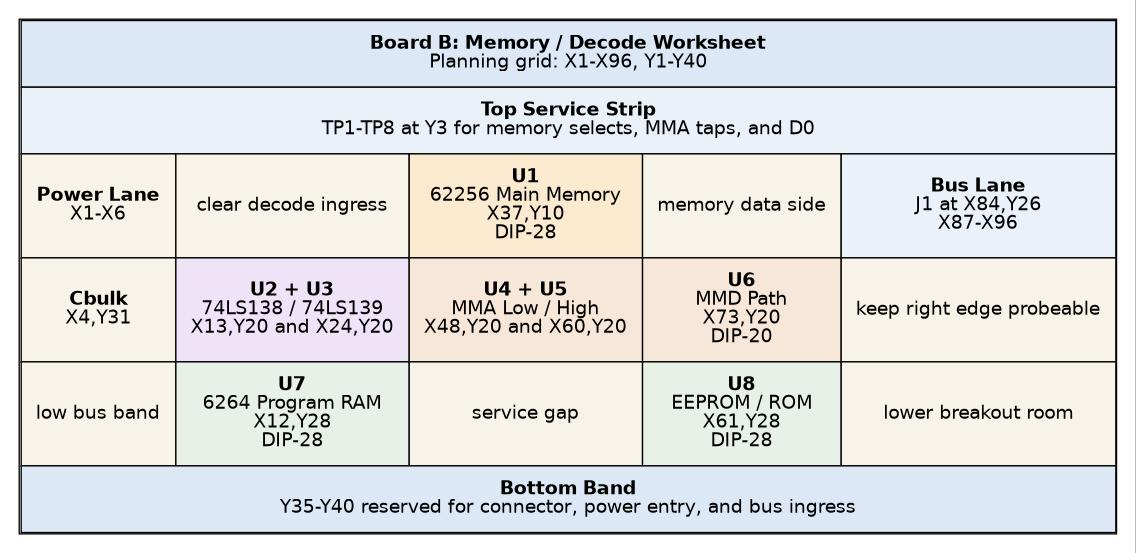
diagrams/RodneyBoardB-worksheet.jpg
