cartheur/aiventure-rodney/diagrams/RodneyBoardB.jpg

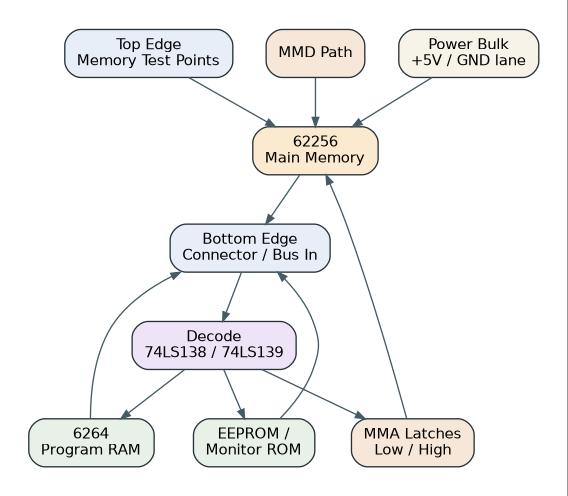
diagrams/RodneyBoardB.jpg
