cartheur/aiventure-rodney/diagrams/RodneyBoardC-silkscreen.jpg

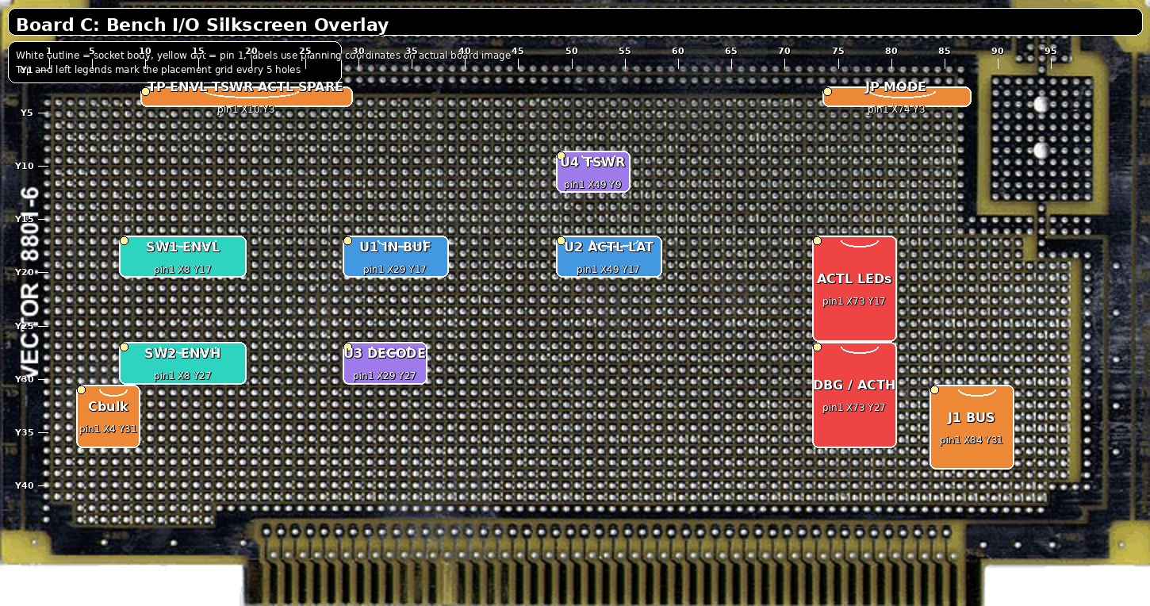
diagrams/RodneyBoardC-silkscreen.jpg
