cartheur/aiventure-rodney/diagrams/RodneyBoardC-worksheet.jpg

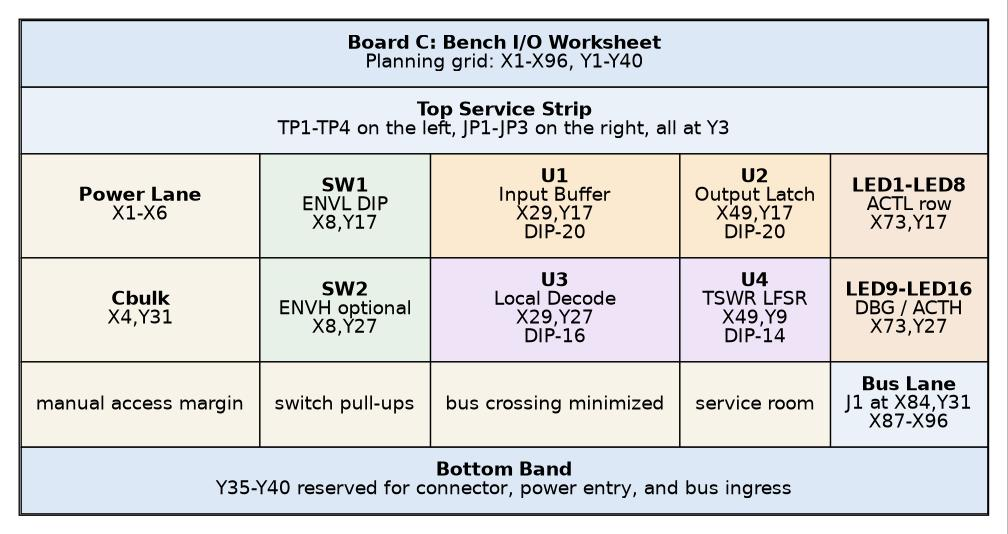
diagrams/RodneyBoardC-worksheet.jpg
