cartheur/aiventure-rodney/diagrams/RodneyBoardC.jpg

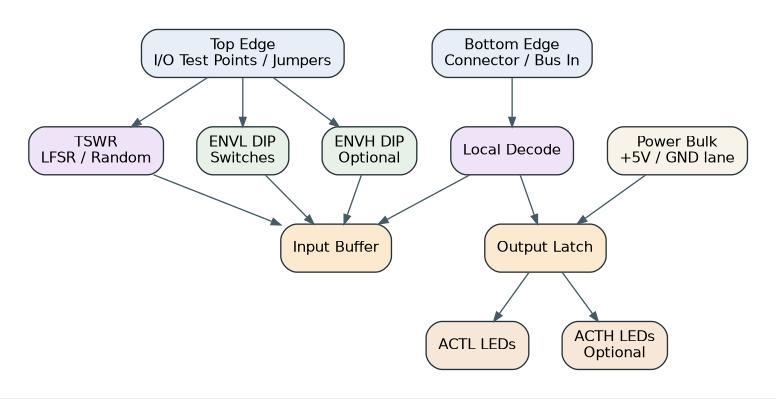
diagrams/RodneyBoardC.jpg
