cartheur/aiventure-rodney/diagrams/RodneySelfProgrammingPath.jpg

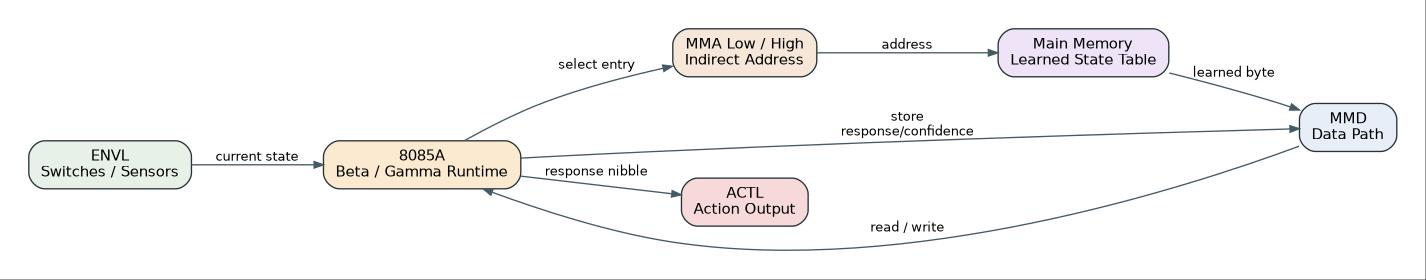
diagrams/RodneySelfProgrammingPath.jpg
