cartheur/aiventure-rodney/diagrams/RodneyWirewrapStack.jpg

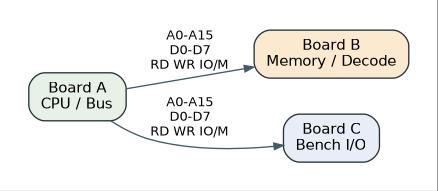
diagrams/RodneyWirewrapStack.jpg
