cartheur/aiventure-rodney/diagrams/RodneyWirewrapWorksheetStack.jpg

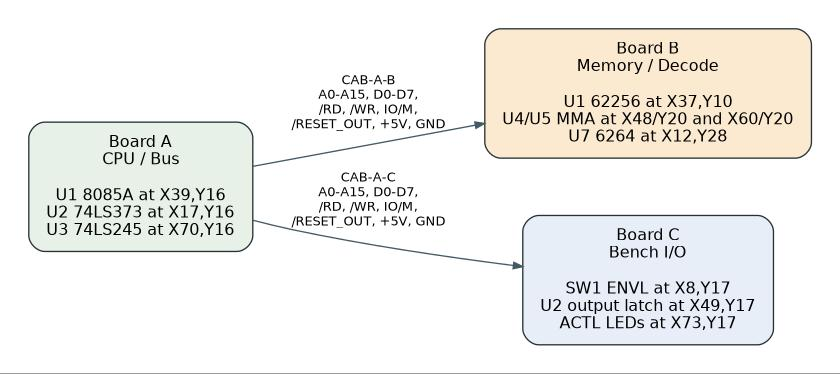
diagrams/RodneyWirewrapWorksheetStack.jpg
