cartheur/aiventure-rodney/diagrams/Vector8801-6-placement-reference.png

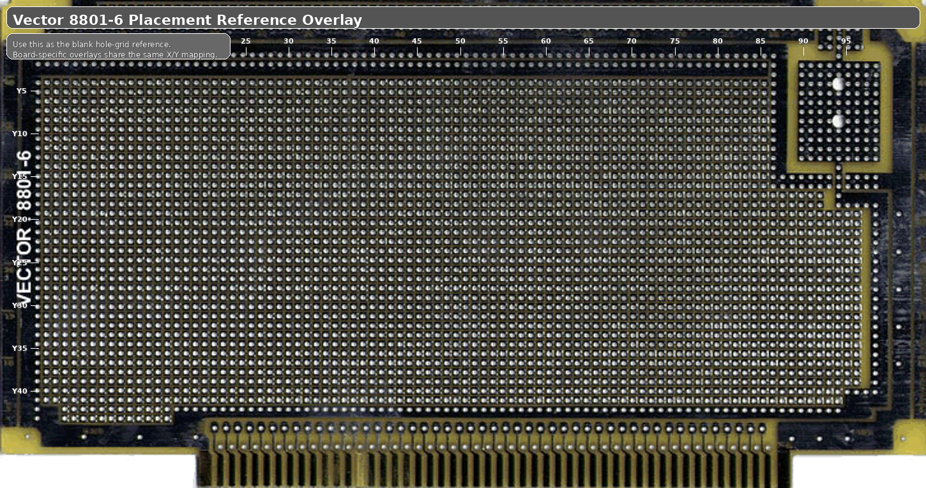
diagrams/Vector8801-6-placement-reference.png
