cartheur/aiventure-rodney/spr-book/0500-text.png

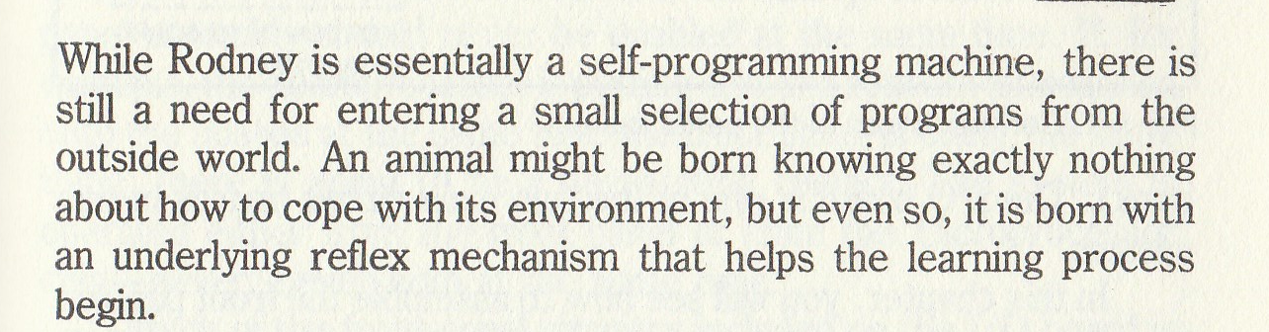
spr-book/0500-text.png
