cartheur/aiventure-rodney/spr-book/0600-text.png

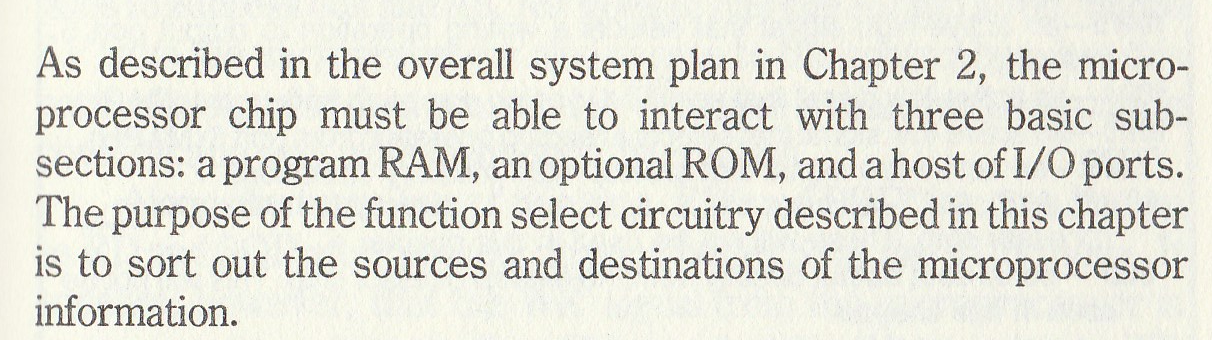
spr-book/0600-text.png
