cartheur/aiventure-rodney/spr-book/0700-text.png

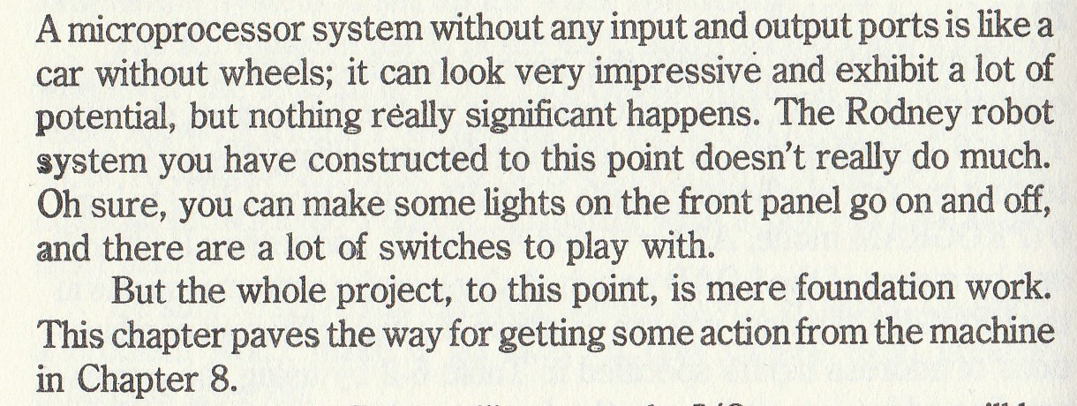
spr-book/0700-text.png
