cartheur/aiventure-rodney/spr-book/0800-text.png

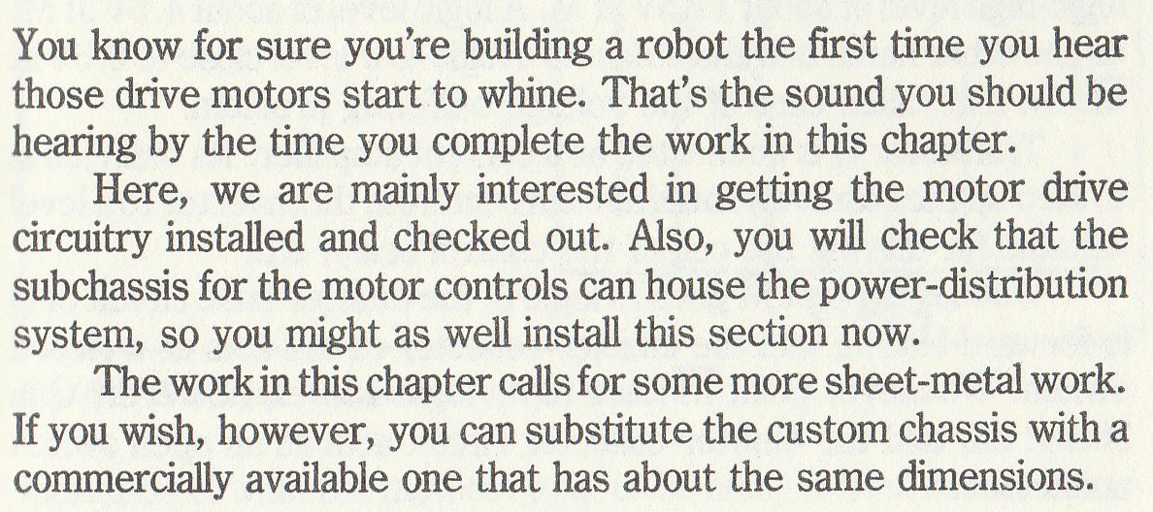
spr-book/0800-text.png
