cartheur/aiventure-rodney/spr-book/0900-text.png

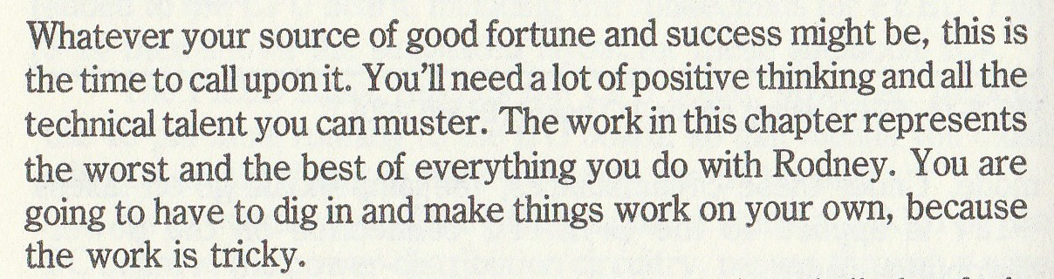
spr-book/0900-text.png
