cartheur/aiventure-rodney/spr-book/0904-2.png

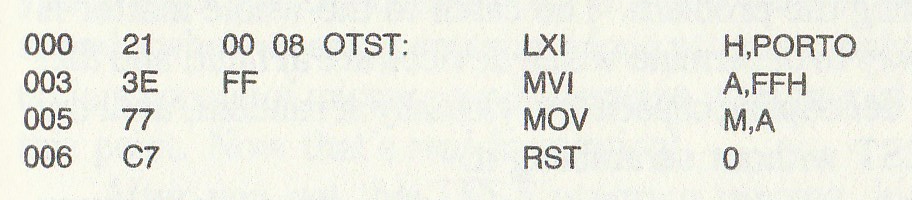
spr-book/0904-2.png
