cartheur/aiventure-rodney/spr-book/0904-3.png

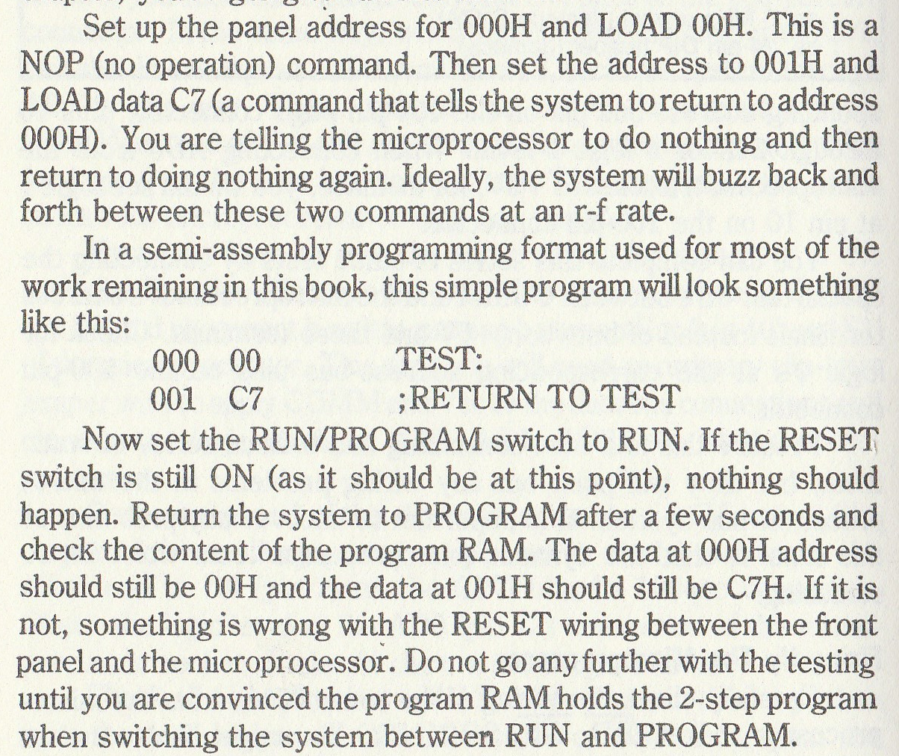
spr-book/0904-3.png
