cartheur/aiventure-rodney/spr-book/0904-4.png

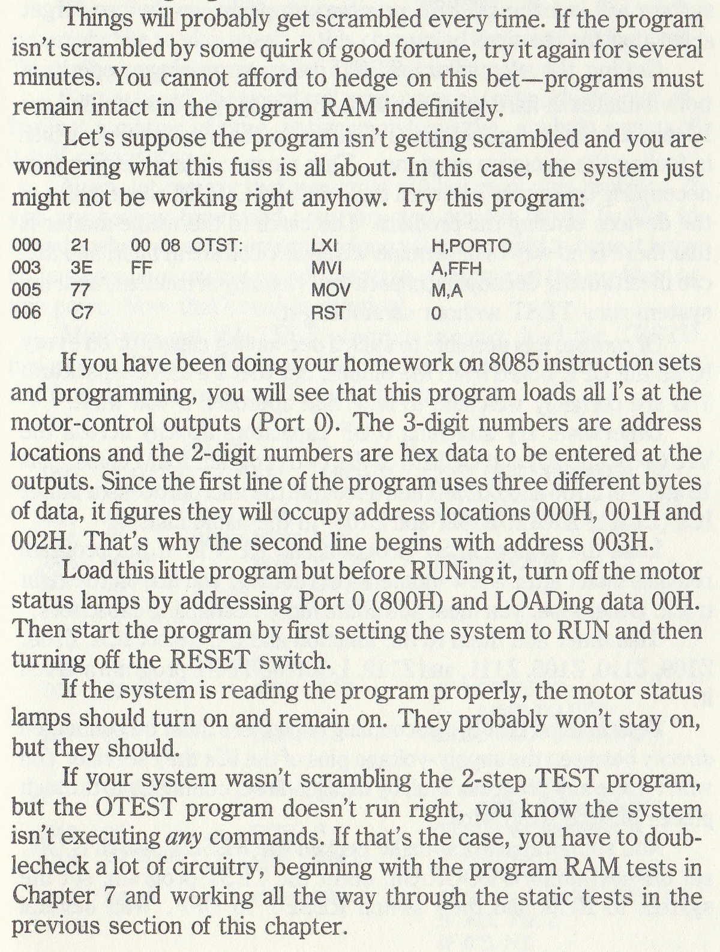
spr-book/0904-4.png
