cartheur/aiventure-rodney/spr-book/0905-1.png

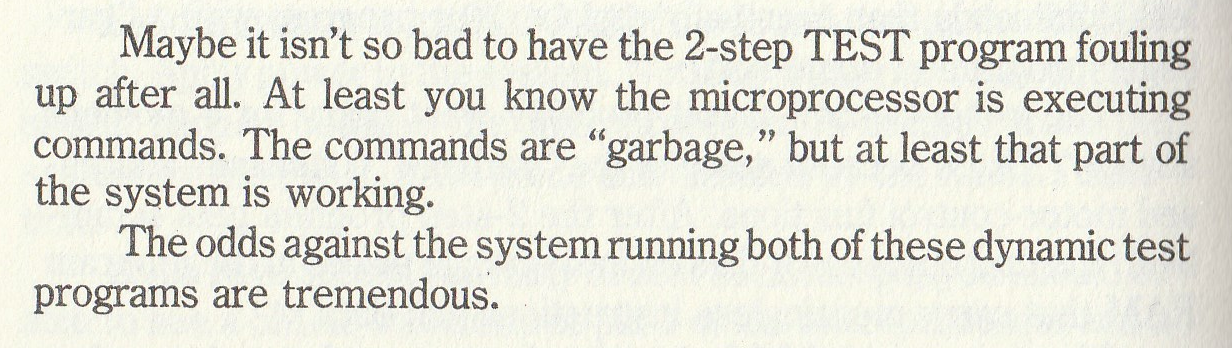
spr-book/0905-1.png
