cartheur/aiventure-rodney/build-of-materials/Parts-List.xlsx

Sheet: rod-y
09 February 2020
Rodney my first scratch-built computer/robot parts list |  | All dimensions in centimeters
Board reference | Table Reference | Part | Part family | Quantity | Component number | Dimension (l) | Dimension (w) | Dimension (h) | Vendor | Vendor Part Number | Price (EUR) | Sample | Picture
 |  | Kynar wire-wrap (WW) wire AWG 24
Auxiliary power supply (NonBuild) | 4.1
Front panel | 5.1
 |  | LED (red) | semiconductors | 8
 |  | LED (yellow) | semiconductors | 4
 |  | LED (green) | semiconductors | 4
 |  | LED (orange) | semiconductors | 4
 |  | LED (blue) | semiconductors | 4
 |  | Cliplite LED mounting (5mm) | other | 20 |  |  |  |  |  |  |  | https://www.allelectronics.com/item/hldcl-c/clear-cliplite-lens/mounting-clip/1.html
 |  | SPST subminature toggle switch | switches | 22
 |  | 16-pin WW IC socket | wire-wrap sockets | 3
 |  | Momentary push-button switch | switches | 1
 |  | 16-conductor DIP jumper | cables | 3
 |  | Aluminum front panel | metal fabrication | 1 |  | 25.40 | 10.16 | 0.20
 |  | Perfboard w/0.25 hole spacing | circuit boards |  |  | 7.60 | 5.10 | n/a
 |  | Kynar WW wire, color [panel board] | wire-wrap wire
I/O board for front-panel ops | 5.2
 |  | 74LS367 hex 3-state buffer | semiconductors | 2 | Z209, Z210
 |  | 7407 hex inverter | semiconductors | 2 | Z211, Z212
 |  | 8226 quad inverting bus transceiver | semiconductors | 2 | Z213, Z214
 |  | 7805 5V 1A regulator | semiconductors | 1 | Z216
 |  | 1000uF, 16WVDC electrolytic | capacitors | 1 | C217
 |  | 22k Ohm 1/4W | resistors | 23
 |  | 150 Ohm, 1/4W | resistors | 20
 |  | 14-pin WW | wire-wrap sockets | 2
 |  | 16-pin WW | wire-wrap sockets | 7
 |  | 24-pin DIP header | wire-wrap headers | 4
 |  | TO-220 heatsink | other parts | 1
 |  | Vector 8801-6 100-pin | circuit boards | 1 |  |  |  |  | Mouser | 574-8801-6 | 50.33
 |  | Vector T46 WW terminal pins | wire-wrap pins | 100 |  | 25.4 | 13.462 |  | Mouser | 574-T46-3-9/C | 13.73
 |  | 50/100 WW connector | wire-wrap connectors | 1
 |  | Kynar WW wire, color [board 2] | wire-wrap wire
CPU board (Part I) | 6.3
 |  | 74LS367 hex 3-state buffer | integrated circuits | 2 | Z103, Z104
 |  | 74LS139 dual 2-line to 4-line decoder | integrated circuits | 1 | Z105
 |  | 74LS138 3-line to 8-line decoder | integrated circuits | 2 | Z108, Z109
 |  | 74LS04 hex inverter | integrated circuits | 2 | Z110, Z111
 |  | 74LS02 quad 2-input NOR gate | integrated circuits | 1 | Z112
 |  | 7805 5V 1A regulator | semiconductors | 1 | Z132
 |  | 1000uF, 16WVDC electrolytic | capacitors | 1 | C101
 |  | 0.1uF mylar | capacitors | 1 | C106
 |  | 14-pin WW | wire-wrap sockets | 3
 |  | 16-pin WW | wire-wrap sockets | 5
 |  | TO-220 heatsink | other parts | 1
 |  | Vector 8801-6 100-pin | circuit boards | 1
 |  | Vector T46 WW terminal pins | wire-wrap pins | 100
 |  | 50/100 WW connector | wire-wrap connectors | 1
 |  | Kynar WW wire, color [board 1] | wire-wrap wire
 | 7.1
CPU board (Part II) | 7.2
 |  | 1024x4 static RAM | integrated circuits | 2 | Z106, Z107
 |  | 74LS373 octal D flip-flop | integrated circuits | 1 | Z115 | Same number?
 |  | 74LS373 hex 3-state buffer | integrated circuits | 2 | Z116, Z117 | Same number?
 |  | 7805 5V 1A regulator | semiconductors | 1 | Z133
 |  | 1000uF, 16WVDC electrolytic | capacitors | 1 | C102
 |  | 0.1uF mylar | capacitors | 1 | C107
 |  | 470k Ohm | resistors | 2 | R250, R251
 |  | 16-pin WW | wire-wrap sockets | 2
 |  | 18-pin WW | wire-wrap sockets | 2
 |  | 20-pin WW | wire-wrap sockets | 1
 |  | 40-pin WW | wire-wrap sockets | 1
 |  | TO-220 heatsink | other parts | 1
 |  | Vector T46 WW terminal pins | wire-wrap pins
 |  | 40-pin DIP cable assembly | cables |  | PC1 |  |  |  |  | Jameco DJ40-1-40
 |  | Kynar wire-wrap (WW) wire | wire-wrap wire
I/O board | 7.4
 |  | 7805 5V 1A regulator | semiconductors | 1 | Z200
 |  | LM3900 quad Norton amplifier | semiconductors | 1 | Z201
 |  | 74LS00 quad 2-input NAND | semiconductors | 1 | Z207
 |  | 74LS93 4-bit binary counter | semiconductors | 1 | Z208
 |  | 7406 hex open-collector inverter | semiconductors | 1 | Z215
 |  | 74LS14 hex Schmitt-trigger interter | semiconductors | 1 | Z206
 |  | 150 Ohm, 1/4W | resistors | 2
 |  | 10k Ohm 1/4W | resistors | 8
 |  | 22k Ohm 1/4W | resistors | 4
 |  | 47k Ohm 1/4W | resistors | 2
 |  | 1M Ohm 1/4W | resistors | 8
 |  | 1000uF, 16WVDC electrolytic | capacitors | 1 | C216
 |  | 0.1uF mylar | capacitors | 1 | C215
 |  | 0.01uF mylar | capacitors | 1 | C217
 |  | 14-pin WW | wire-wrap sockets | 5
 |  | 24-pin WW | wire-wrap sockets | 2
 |  | 40-pin WW | wire-wrap sockets | 1
 |  | TO-220 heatsink | other parts | 1
 |  | Vector T46 WW terminal pins | wire-wrap pins
 |  | 24-pin DIP header | wire-wrap headers | 2
Power distribution and motor control | 8.2
 |  | 2N4402 PNP | transistors | 4 | Q301-Q304
 |  | 1N458 rectifier diode | semiconductors | 4 | D301-D304
 |  | LED (blue) | semiconductors | 4 | L301-L304
 |  | 5.1V 400mW zener diode | semiconductors | 1 | ZD301
 |  | 6A, 50V bridge rectifier | semiconductors | 1 | BR300
 |  | 1k Ohm 1/4W | resistors | 4 | R301-R304
 |  | 820 Ohm 1/4W | resistors | 4 | R305-R308
 |  | 150 Ohm, 1/4W | resistors | 4 | R309-R312
 |  | 470 Ohm 1/2W | resistors | 1 | R300
 |  | 0.1uF mylar | capacitors | 2 | C301, C302
 |  | 12V DPDT relay. 10A contacts | relays | 4 | RL301-RL304
 |  | 12 VDC motor | motors | 2 | M1, M2 |  |  |  |  | #5-936 (Sub.5-1660)
 |  | SPST switch | switches | 1 | S301
 |  | 8-terminal barrier strip | other parts | 2 | TS300, TS301 |  |  |  |  | RS #274-670
 |  | Vector T46 WW terminal pins | wire-wrap pins | 18
 |  | 5A slow-blow fuses | other parts | 2 | F301, F302 |  |  |  |  | RS #270-1287
 |  | Fuseholder | other parts | 2
 |  | Cliplite LED mounting (5mm) | other parts | 4
 |  | AWG18 stranded wire
 |  | AWG22 solid hook-up wire
 |  | Kynar wire-wrap (WW) wire
 |  | Single-side PC stock |  | 1 |  | 7.62 | 10.16
 |  | Aluminum stock |  | 1 |  | 24.13 | 17.78
 |  | Transistor mounting sockets |  | 4 |  |  |  |  |  | RS #276-548
CPU board (Part III) | 9.1
 |  | 8085 8-bit microprocessor |  | 1 | Z100
 |  | 8216 quad bus transceiver |  | 2 | Z1011, Z1012
 |  | 74LS373 octal latch |  | 1 | Z102 | Same number?
 |  | 2.7k Ohm 1/4W | resistors | 3
 |  | 22pF ceramic | capacitors | 2
 |  | 0.1uF mylar | capacitors | 2 |  | See text for explanation
 |  | 16-pin WW | wire-wrap sockets | 2
 |  | 20-pin WW | wire-wrap sockets | 1
 |  | 24-pin WW | wire-wrap sockets | 1
 |  | 40-pin WW | wire-wrap sockets | 1
 |  | 5MHz crystal |  | 1 |  |  |  |  |  | Jameco CY7A
 |  | 24-pin DIP header | wire-wrap headers | 1
Battery recharging system | 9.2
 |  | 12V 14Ah battery |  | 1 |  |  |  |  |  | Sears #28K44314N
 |  | 12V 4A battery charger |  | 1 |  |  |  |  |  | Sears #28K7126
 |  | Battery charger current limiter |  | 1 |  |  |  |  |  | Sears #28K7104
CPU board (Part IV) | 11.1
 |  | 74LS373 8-bit latch |  | 2
 |  | 74LS367 hex buffer |  | 4
 |  | 2141 4096x1 static RAM |  | 8
 |  | 100uF 16WVDC electrolytic | capacitors | 1 | C108
Mini-tape interface circuit and tape program ROM | 13.1
 |  | LM324 quad operational amplifier |  | 1 | Z210
 |  | 14-pin WW | wire-wrap sockets | 1
 |  | 100 Ohm 1/2W | resistors | 1
 |  | 220 Ohm 1/2W | resistors | 1
 |  | 820 Ohm 1/2W | resistors | 1
 |  | 1k Ohm 1/4W | resistors | 3
 |  | 10k Ohm 1/4W | resistors | 6
 |  | 22k Ohm 1/4W | resistors | 1
 |  | 1M Ohm 1/4W | resistors | 1
 |  | 0.001uF mylar | capacitors | 1
 |  | 0.1uF mylar | capacitors | 3
 |  | 1N458 rectifier diode | semiconductors | 2
PROM components to be added to CPU board (Board 100)
 |  | 1702 256x8 PROM |  | 1 | Z131
 |  | 24-pin WW | wire-wrap sockets | 1

Sheet: vendors
Vendor | Location | Web | Key
Vector Electronics |  |  | VC
Mike’s Electronics |  | https://www.mikeselectronicparts.com | ME
Pheonix Enterprises |  | https://www.peconnectors.com | PE
Surplus Center |  | https://www.surpluscenter.com | SC
Mouser EU |  | https://nl.mouser.com | MU

Sheet: family
cables
capacitors
circuit boards
integrated circuits
metal fabrication
motors
other parts
relays
resistors
semiconductors
switches
transistors
wire-wrap connectors
wire-wrap headers
wire-wrap pins
wire-wrap wire
wire-wrap sockets

Sheet: Complete parts list
Table Reference | Part | Quantity | Schematic number
 | Kynar wire-wrap (WW) wire AWG ??
4.1
5.1
 | LED (red) | 8
 | LED (yellow) | 4
 | LED (green) | 4
 | LED (white) | 4
 | Cliplite LED mounting (5mm) | 20
 | SPST subminature toggle switch | 22
 | 16-pin WW socket | 3
 | Momentary push-button switch | 1
 | 16-conductor DIP jumper | 3
 | Aluminum front panel | 1
 | Perfboard w/0.25 hole spacing
 | Kynar WW wire, color [panel board]
5.2
 | 74LS367 hex 3-state buffer | 2 | Z209, Z210
 | 7407 hex inverter | 2 | Z211, Z212
 | 8226 quad inverting bus transceiver | 2 | Z213, Z214
 | 7805 5V 1A regulator | 1 | Z216
 | 1000uF, 16WVDC electrolytic | 1 | C217
 | 22k Ohm 1/4W | 23
 | 150 Ohm, 1/4W | 20
 | 14-pin WW | 2
 | 16-pin WW | 7
 | 24-pin DIP header | 4
 | TO-220 heatsink | 1
 | Vector 8801-6 100-pin | 1
 | Vector T46 WW terminal pins | 100
 | 50/100 WW connector | 1
 | Kynar WW wire, color [board 2]
6.3
 | 74LS367 hex 3-state buffer | 2 | Z103, Z104
 | 74LS139 dual 2-line to 4-line decoder | 1 | Z105
 | 74LS138 3-line to 8-line decoder | 2 | Z108, Z109
 | 74LS04 hex inverter | 2 | Z110, Z111
 | 74LS02 quad 2-input NOR gate | 1 | Z112
 | 7805 5V 1A regulator | 1 | Z132
 | 1000uF, 16WVDC electrolytic | 1 | C101
 | 0.1uF mylar | 1 | C106
 | 14-pin WW | 3
 | 16-pin WW | 5
 | TO-220 heatsink | 1
 | Vector 8801-6 100-pin | 1
 | Vector T46 WW terminal pins | 100
 | 50/100 WW connector | 1
 | Kynar WW wire, color [board 1]
7.1
7.2
 | 1024x4 static RAM | 2 | Z106, Z107
 | 74LS373 octal D flip-flop | 1 | Z115
 | 74LS373 hex 3-state buffer | 2 | Z116, Z117
 | 7805 5V 1A regulator | 1 | Z133
 | 1000uF, 16WVDC electrolytic | 1 | C102
 | 0.1uF mylar | 1 | C107
 | 470k Ohm | 2 | R250, R251
 | 16-pin WW | 2
 | 18-pin WW | 2
 | 20-pin WW | 1
 | 40-pin WW | 1
 | TO-220 heatsink | 1
 | Vector T46 WW terminal pins
 | 40-pin DIP cable assembly |  | PC1
 | Kynar wire-wrap (WW) wire
7.4
 | 7805 5V 1A regulator | 1 | Z200
 | LM3900 quad Norton amplifier | 1 | Z201
 | 74LS00 quad 2-input NAND | 1 | Z207
 | 74LS93 4-bit binary counter | 1 | Z208
 | 7406 hex open-collector inverter | 1 | Z215
 | 74LS14 hex Schmitt-trigger interter | 1 | Z206
 | 150 Ohm, 1/4W | 2
 | 10k Ohm 1/4W | 8
 | 22k Ohm 1/4W | 4
 | 47k Ohm 1/4W | 2
 | 1M Ohm 1/4W | 8
 | 1000uF, 16WVDC electrolytic | 1 | C216
 | 0.1uF mylar | 1 | C215
 | 0.01uF mylar | 1 | C217
 | 14-pin WW | 5
 | 24-pin WW | 2
 | 40-pin WW | 1
 | TO-220 heatsink | 1
 | Vector T46 WW terminal pins
 | 24-pin DIP header | 2
8.2
 | 2N4402 PNP | 4 | Q301-Q304
 | 1N458 rectifier diode | 4 | D301-D304
 | LED (check this) | 4 | L301-L304
 | 5.1V 400mW zener diode | 1 | ZD301
 | 6A, 50V bridge rectifier | 1 | BR300
 | 1k Ohm 1/4W | 4 | R301-R304
 | 820 Ohm 1/4W | 4 | R305-R308
 | 150 Ohm, 1/4W | 4 | R309-R312
 | 470 Ohm 1/2W | 1 | R300
 | 0.1uF mylar | 2 | C301, C302
 | 12V DPDT relay. 10A contacts | 4 | RL301-RL304
 | 12 VDC motor | 2 | M1, M2
 | SPST switch | 1 | S301
 | 8-terminal barrier strip | 2 | TS300, TS301
 | Vector T46 WW terminal pins | 18
 | 5A slow-blow fuses | 2 | F301, F302
 | Fuseholder | 2
 | Cliplite LED mounting (5mm) | 4
 | AWG18 stranded wire
 | AWG22 solid hook-up wire
 | Kynar wire-wrap (WW) wire
 | Single-side PC stock | 1
 | Aluminum stock | 1
 | Transistor mounting sockets | 4
9.1
 | 8085 8-bit microprocessor | 1 | Z100
 | 8216 quad bus transceiver | 2 | Z1011, Z1012
 | 74LS373 octal latch | 1 | Z102
 | 2.7k Ohm 1/4W | 3
 | 22pF ceramic | 2
 | 0.1uF mylar | 2
 | 16-pin WW | 2
 | 20-pin WW | 1
 | 24-pin WW | 1
 | 40-pin WW | 1
 | 5MHz crystal | 1
 | 24-pin DIP header | 1
9.2
 | 12V 14Ah battery | 1
 | 12V 4A battery charger | 1
 | Battery charger current limiter | 1
11.1
 | 74LS373 8-bit latch | 2
 | 74LS367 hex buffer | 4
 | 2141 4096x1 static RAM | 8
 | 100uF 16WVDC electrolytic | 1 | C108
13.1
 | LM324 quad operational amplifier | 1 | Z210
 | 14-pin WW | 1
 | 100 Ohm 1/2W | 1
 | 220 Ohm 1/2W | 1
 | 820 Ohm 1/2W | 1
 | 1k Ohm 1/4W | 3
 | 10k Ohm 1/4W | 6
 | 22k Ohm 1/4W | 1
 | 1M Ohm 1/4W | 1
 | 0.001uF mylar | 1
 | 0.1uF mylar | 3
 | 1N458 rectifier diode | 2
 | 1702 256x8 PROM | 1 | Z131
 | 24-pin WW | 1

Sheet: WW headers-sockets
24-pin DIP header | 2
14-pin WW | 11
16-pin WW | 19
18-pin WW | 2
20-pin WW | 2
24-pin WW | 3
40-pin WW | 3

Sheet: Printed list
26 July 2020
Rodney: Part correlation chart - can we state clearly that the parts are in hand?
Board reference | Table Ref. | Part | Part family | Quantity | Component # | Have? | Remainders | Due
 |  | Kynar wire-wrap (WW) wire AWG 24
Auxiliary power supply (for the Nest) | 4.1
Front panel | 5.1
 |  | LED (red) | semiconductors | 8
 |  | LED (yellow) | semiconductors | 4
 |  | LED (green) | semiconductors | 4
 |  | LED (orange) | semiconductors | 4
 |  | LED (blue) | semiconductors | 4
 |  | Cliplite LED mounting (5mm) | other | 20
 |  | SPST subminature toggle switch | switches | 22
 |  | 16-pin WW IC socket | wire-wrap sockets | 3
 |  | Momentary push-button switch | switches | 1
 |  | 16-conductor DIP jumper | cables | 3
 |  | Aluminum front panel | metal fabrication | 1
 |  | Perfboard w/0.25 hole spacing | circuit boards
 |  | Kynar WW wire, color [panel board] | wire-wrap wire
I/O board for front-panel ops | 5.2
 |  | 74LS367 hex 3-state buffer | semiconductors | 2 | Z209, Z210
 |  | 7407 hex inverter | semiconductors | 2 | Z211, Z212
 |  | 74LS242 quad inverting bus transceiver | semiconductors | 2 | Z213, Z214 | X | 4
 |  | 7805 5V 1A regulator | semiconductors | 1 | Z216
 |  | 1000uF, 16WVDC electrolytic | capacitors | 1 | C217
 |  | 22k Ohm 1/4W | resistors | 23
 |  | 150 Ohm, 1/4W | resistors | 20
 |  | 14-pin WW | wire-wrap sockets | 2
 |  | 16-pin WW | wire-wrap sockets | 7
 |  | 24-pin DIP header | wire-wrap headers | 4
 |  | TO-220 heatsink | other parts | 1
 |  | Vector 8801-6 100-pin | circuit boards | 1
 |  | Vector T46 WW terminal pins | wire-wrap pins | 100
 |  | 50/100 WW connector | wire-wrap connectors | 1
 |  | Kynar WW wire, color [board 2] | wire-wrap wire
CPU board (Part I) | 6.3
 |  | 74LS367 hex 3-state buffer | integrated circuits | 2 | Z103, Z104
 |  | 74LS139 dual 2-line to 4-line decoder | integrated circuits | 1 | Z105
 |  | 74LS138 3-line to 8-line decoder | integrated circuits | 2 | Z108, Z109
 |  | 74LS04 hex inverter | integrated circuits | 2 | Z110, Z111
 |  | 74LS02 quad 2-input NOR gate | integrated circuits | 1 | Z112
 |  | 7805 5V 1A regulator | semiconductors | 1 | Z132
 |  | 1000uF, 16WVDC electrolytic | capacitors | 1 | C101
 |  | 0.1uF mylar | capacitors | 1 | C106
 |  | 14-pin WW | wire-wrap sockets | 3
 |  | 16-pin WW | wire-wrap sockets | 5
 |  | TO-220 heatsink | other parts | 1
 |  | Vector 8801-6 100-pin | circuit boards | 1
 |  | Vector T46 WW terminal pins | wire-wrap pins | 100
 |  | 50/100 WW connector | wire-wrap connectors | 1
 |  | Kynar WW wire, color [board 1] | wire-wrap wire
 | 7.1
CPU board (Part II) | 7.2
 |  | 2114 - 1024x4 static RAM | integrated circuits | 2 | Z106, Z107 | X | 4
 |  | 74LS373 octal D flip-flop | integrated circuits | 1 | Z115
 |  | 74LS373 hex 3-state buffer | integrated circuits | 2 | Z116, Z117
 |  | 7805 5V 1A regulator | semiconductors | 1 | Z133
 |  | 1000uF, 16WVDC electrolytic | capacitors | 1 | C102
 |  | 0.1uF mylar | capacitors | 1 | C107
 |  | 470k Ohm | resistors | 2 | R250, R251
 |  | 16-pin WW | wire-wrap sockets | 2
 |  | 18-pin WW | wire-wrap sockets | 2
 |  | 20-pin WW | wire-wrap sockets | 1
 |  | 40-pin WW | wire-wrap sockets | 1
 |  | TO-220 heatsink | other parts | 1
 |  | Vector T46 WW terminal pins | wire-wrap pins
 |  | 40-pin DIP cable assembly | cables |  | PC1
 |  | Kynar wire-wrap (WW) wire | wire-wrap wire
I/O board | 7.4
 |  | 7805 5V 1A regulator | semiconductors | 1 | Z200
 |  | LM3900 quad Norton amplifier | semiconductors | 1 | Z201
 |  | 74LS00 quad 2-input NAND | semiconductors | 1 | Z207
 |  | 74LS93 4-bit binary counter | semiconductors | 1 | Z208
 |  | 7406 hex open-collector inverter | semiconductors | 1 | Z215
 |  | 74LS14 hex Schmitt-trigger interter | semiconductors | 1 | Z206
 |  | 150 Ohm, 1/4W | resistors | 2
 |  | 10k Ohm 1/4W | resistors | 8
 |  | 22k Ohm 1/4W | resistors | 4
 |  | 47k Ohm 1/4W | resistors | 2
 |  | 1M Ohm 1/4W | resistors | 8
 |  | 1000uF, 16WVDC electrolytic | capacitors | 1 | C216
 |  | 0.1uF mylar | capacitors | 1 | C215
 |  | 0.01uF mylar | capacitors | 1 | C217
 |  | 14-pin WW | wire-wrap sockets | 5
 |  | 24-pin WW | wire-wrap sockets | 2
 |  | 40-pin WW | wire-wrap sockets | 1
 |  | TO-220 heatsink | other parts | 1
 |  | Vector T46 WW terminal pins | wire-wrap pins
 |  | 24-pin DIP header | wire-wrap headers | 2
Power distribution and motor control | 8.2
 |  | 2N4402 PNP | transistors | 4 | Q301-Q304
 |  | 1N458 rectifier diode | semiconductors | 4 | D301-D304
 |  | LED (blue) | semiconductors | 4 | L301-L304
 |  | 5.1V 400mW zener diode | semiconductors | 1 | ZD301
 |  | 6A, 50V bridge rectifier | semiconductors | 1 | BR300
 |  | 1k Ohm 1/4W | resistors | 4 | R301-R304
 |  | 820 Ohm 1/4W | resistors | 4 | R305-R308
 |  | 150 Ohm, 1/4W | resistors | 4 | R309-R312
 |  | 470 Ohm 1/2W | resistors | 1 | R300
 |  | 0.1uF mylar | capacitors | 2 | C301, C302
 |  | 12V DPDT relay. 10A contacts | relays | 4 | RL301-RL304
 |  | 12 VDC motor | motors | 2 | M1, M2
 |  | SPST switch | switches | 1 | S301
 |  | 8-terminal barrier strip | other parts | 2 | TS300, TS301
 |  | Vector T46 WW terminal pins | wire-wrap pins | 18
 |  | 5A slow-blow fuses | other parts | 2 | F301, F302
 |  | Fuseholder | other parts | 2
 |  | Cliplite LED mounting (5mm) | other parts | 4
 |  | AWG18 stranded wire
 |  | AWG22 solid hook-up wire
 |  | Kynar wire-wrap (WW) wire
 |  | Single-side PC stock |  | 1
 |  | Aluminum stock |  | 1
 |  | Transistor mounting sockets |  | 4
CPU board (Part III) | 9.1
 |  | 8085 8-bit microprocessor |  | 1 | Z100
 |  | 8216 quad bus transceiver |  | 2 | Z1011, Z1012
 |  | 74LS373 octal latch |  | 1 | Z102
 |  | 2.7k Ohm 1/4W | resistors | 3
 |  | 22pF ceramic | capacitors | 2
 |  | 0.1uF mylar | capacitors | 2
 |  | 16-pin WW | wire-wrap sockets | 2
 |  | 20-pin WW | wire-wrap sockets | 1
 |  | 24-pin WW | wire-wrap sockets | 1
 |  | 40-pin WW | wire-wrap sockets | 1
 |  | 5MHz crystal |  | 1
 |  | 24-pin DIP header | wire-wrap headers | 1
Battery recharging system | 9.2
 |  | 12V 18Ah battery |  | 1
 |  | 12V 4A battery charger |  | 1
 |  | Battery charger current limiter |  | 1
CPU board (Part IV) | 11.1
 |  | 74LS373 8-bit latch |  | 2
 |  | 74LS367 hex buffer |  | 4
 |  | SY2147H 4096x1 static RAM |  | 8 |  | X | 10
 |  | 100uF 16WVDC electrolytic | capacitors | 1 | C108
Mini-tape interface circuit and | 13.1
tape program ROM |  | LM324 quad operational amplifier |  | 1 | Z210
 |  | 14-pin WW | wire-wrap sockets | 1
 |  | 100 Ohm 1/2W | resistors | 1
 |  | 220 Ohm 1/2W | resistors | 1
 |  | 820 Ohm 1/2W | resistors | 1
 |  | 1k Ohm 1/4W | resistors | 3
 |  | 10k Ohm 1/4W | resistors | 6
 |  | 22k Ohm 1/4W | resistors | 1
 |  | 1M Ohm 1/4W | resistors | 1
 |  | 0.001uF mylar | capacitors | 1
 |  | 0.1uF mylar | capacitors | 3
 |  | 1N458 rectifier diode | semiconductors | 2
PROM components to be
added to CPU board (Board 100)
 |  | 1702 256x8 PROM |  | 1 | Z131
 |  | 24-pin WW | wire-wrap sockets | 1
