cartheur/aiventure-rodney/build-of-materials/BOM_Rodney.csv

ID | Name | Designator | Quantity | Part Number | Manufacturer | Supplier | Supplier Part Number | Unit Price (EUR)
1 | 22k |  | 28 | MFR-25FBF52-22K | Yageo | Mouser | 603-MFR-25FBF52-22K | 0.093
2 | 150R |  | 22 | MFR25SFRF52-150R | Yageo | Mouser | 603-MFR25SFRF52-150R | 0.093
3 | 1000uF | C101,C102,C216,C217? | 4 | ESK108M016AH2AA | Kemet | Mouser | 80-ESK108M016AH2AA | 0.316
4 | DIP24WW | DIP-Header | 8 | 123-43-624-41-001000 | MillMax | Mouser | 575-12343624 | 7.76
5 | 0.1uF | C106,C107,OTH | 7 | QYX2A104KTP | Nichicon | Mouser | 647-QYX2A103KTP | 0.502
6 | 470k | R250,R251 | 2 | MFR-25FBF52-470K | Yageo | Mouser | 603-MFR-25FBF52-470K | 0.093
7 | 47k |  | 2 | MFR-25FBF52-47K | Yageo | Mouser | 603-MFR-25FBF52-47K | 0.093
8 | 10k |  | 14 | MFR-25FBF52-10K | Yageo | Mouser | 603-MFR-25FBF52-10K | 0.093
9 | 1M |  | 9 | MFR-25FBF52-1M | Yageo | Mouser | 603-MFR-25FBF52-1M | 0.093
10 | 0.01uF | C217? | 1 | QYX2A103KTP | Nichicon | Mouser | 647-QYX2A103KTP | 0.372
11 | 2.7k |  | 3 | MFR-25FBF52-27K | Yageo | Mouser | 603-MFR-25FBF52-27K | 0.093
12 | 22pF |  | 2 | K220J15C0GF5TH5 | Vishay | Mouser | 594-K220J15C0GF5TH5 | 0.214
13 | 5MHz-STD | X100 | 1 | MXO45HS-3C-5M0000 | CTS | Mouser | 774-MXO45HS-3C-5.0 | 3.61
14 | 100uF | C108 | 1 | ESK107M016AC3AA | Kemet | Mouser | 80-ESK107M016AC3AA | 0.158
15 | LM324 | Z210 | 1 | LM324AN | Texas Instruments | Mouser | 595-LM324AN | 0.326
16 | 1N458 |  | 2 | 1N458ATR | Fairchild | Mouser | 512-1N458ATR | 0.195
17 | 0.001uF |  | 1 | QYX2A102KTP | Nichicon | Mouser | 647-QYX2A102KTP | 0.353
18 | 1k |  | 3 | MFR-25FBF52-1K | Yageo | Mouser | 603-MFR-25FBF52-1K | 0.093
19 | 100R |  | 1 | MFR-25FBF52-100R | Yageo | Mouser | 603-MFR-25FBF52-100R | 0.093
20 | 220R |  | 1 | MFR-25FBF52-220R | Yageo | Mouser | 603-MFR-25FBF52-220R | 0.093
21 | 820R |  | 1 | MFR-25FBF52-820R | Yageo | Mouser | 603-MFR-25FBF52-820R | 0.093
22 | 256x8 | Z131 | 1 | AT27C020-55PU | Microchip | Mouser | 556-AT27C020-55PU | 5.13
23 | DIP32WW |  | 1 | 32-6501-30 | Aries | Mouser | 535-32-6501-30 | 10.26
