cartheur/aiventure-rodney/build-of-materials/datasheets/July-Order/dip-header.jpg

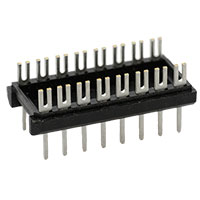
build-of-materials/datasheets/July-Order/dip-header.jpg
