cartheur/aiventure-rodney/build-of-materials/datasheets/cliplite-led-mounts.jpg

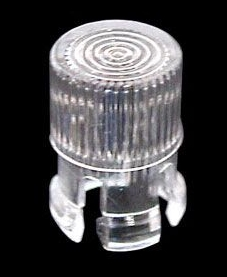
build-of-materials/datasheets/cliplite-led-mounts.jpg
