cartheur/aiventure-rodney/build-of-materials/datasheets/ges/bp12a18.jpg

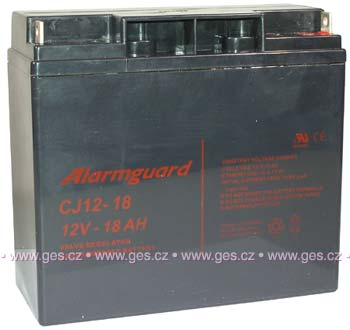
build-of-materials/datasheets/ges/bp12a18.jpg
