cartheur/aiventure-rodney/build-of-materials/datasheets/integrated-circuits/intel/P8085.jpg

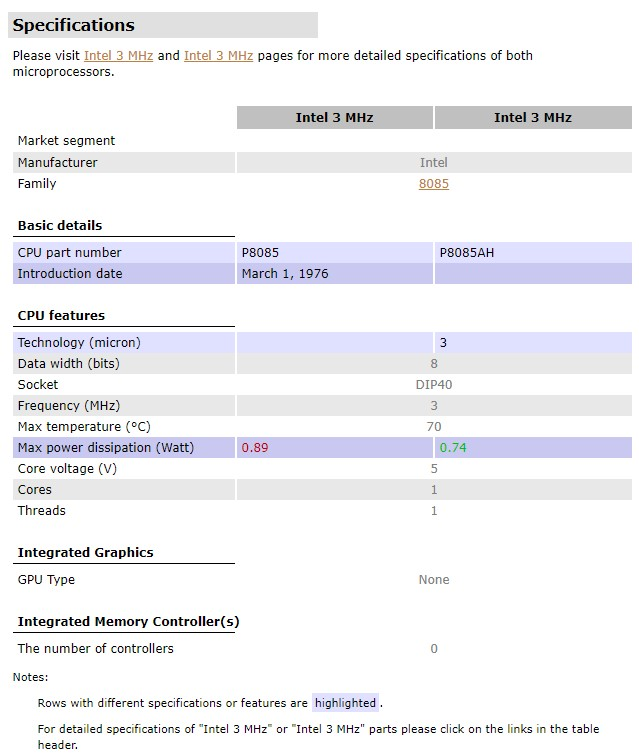
build-of-materials/datasheets/integrated-circuits/intel/P8085.jpg
