cartheur/aiventure-rodney/build-of-materials/datasheets/mts243.jpg

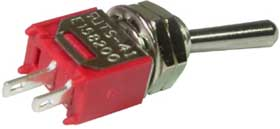
build-of-materials/datasheets/mts243.jpg
