cartheur/aiventure-rodney/build-of-materials/datasheets/quotes/spooky-too.jpg

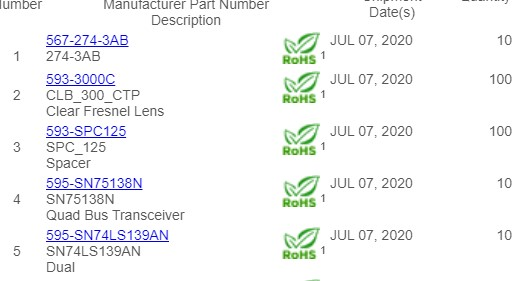
build-of-materials/datasheets/quotes/spooky-too.jpg
