cartheur/aiventure-rodney/build-of-materials/datasheets/quotes/spooky.jpg

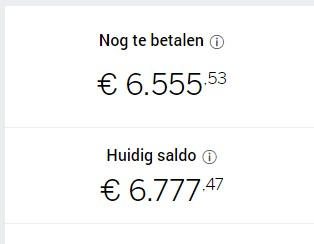
build-of-materials/datasheets/quotes/spooky.jpg
