cartheur/aiventure-rodney/build-of-materials/datasheets/switchcraft/ai8100t.jpg

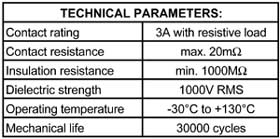
build-of-materials/datasheets/switchcraft/ai8100t.jpg
