cartheur/aiventure-rodney/build-of-materials/datasheets/switchcraft/ams243d.jpg

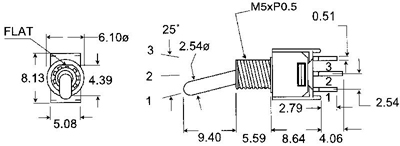
build-of-materials/datasheets/switchcraft/ams243d.jpg
