cartheur/aiventure-rodney/build-of-materials/datasheets/switchcraft/mts500ap.jpg

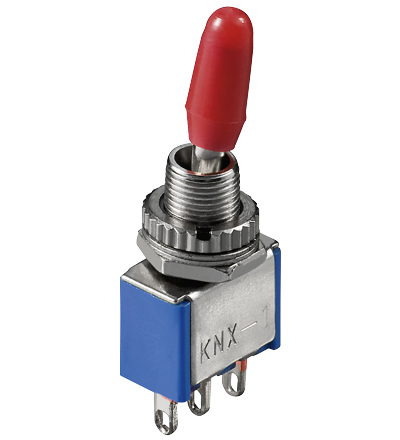
build-of-materials/datasheets/switchcraft/mts500ap.jpg
