cartheur/aiventure-rodney/build-of-materials/datasheets/switchcraft/mts500apd.jpg

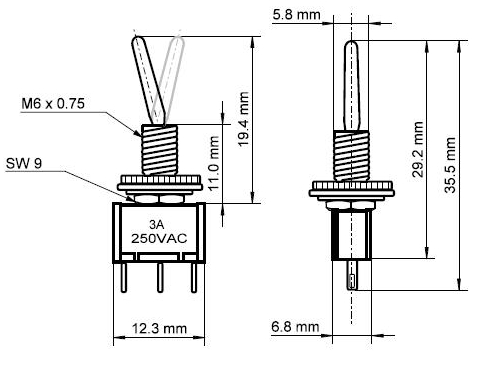
build-of-materials/datasheets/switchcraft/mts500apd.jpg
