cartheur/aiventure-rodney/build-of-materials/datasheets/switchcraft/s-l1600.jpg

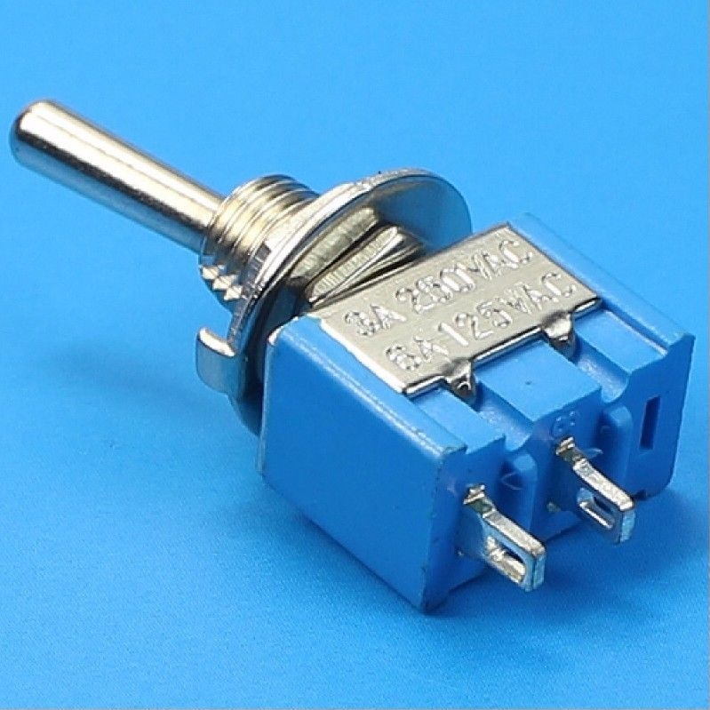
build-of-materials/datasheets/switchcraft/s-l1600.jpg
