cartheur/aiventure-rodney/build-of-materials/datasheets/vector/K24A.jpg

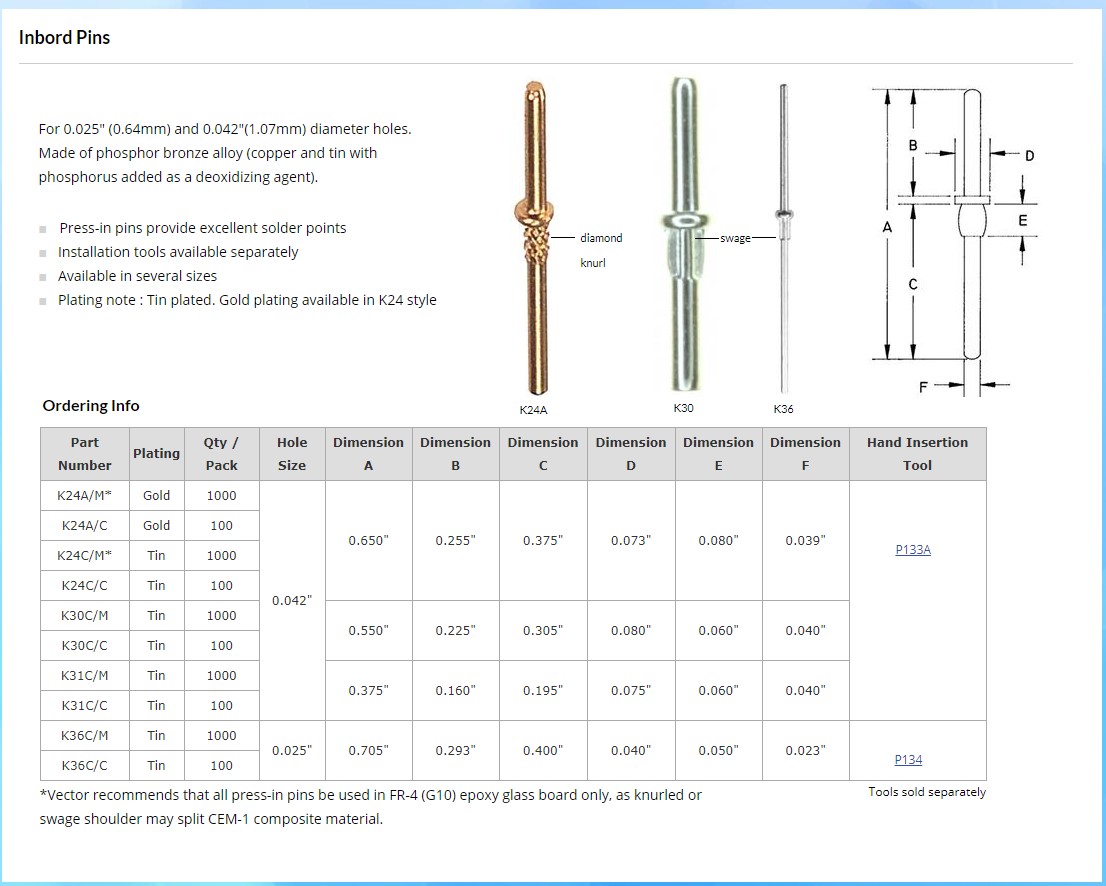
build-of-materials/datasheets/vector/K24A.jpg
