cartheur/aiventure-rodney/build/5-front-panel/images/assembled-panel.png

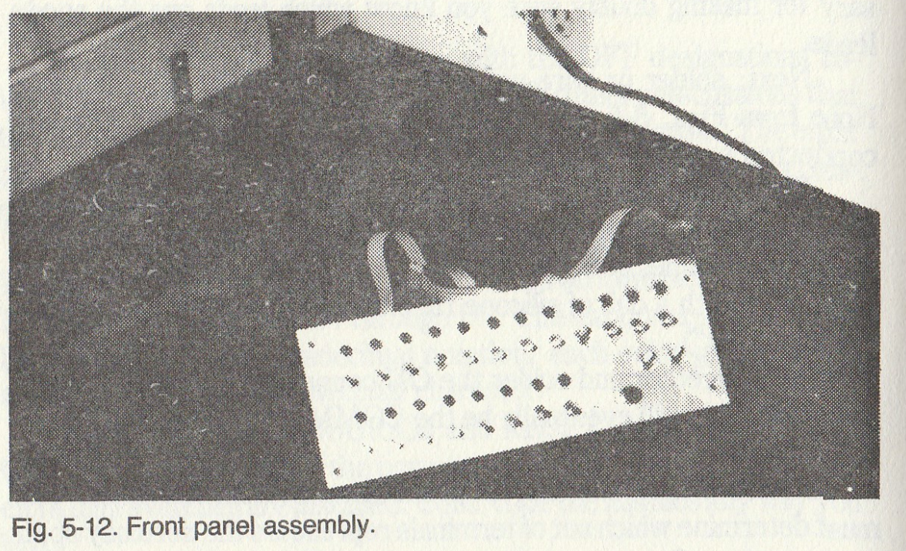
build/5-front-panel/images/assembled-panel.png
