cartheur/aiventure-rodney/build/5-front-panel/images/fig.5-9.png

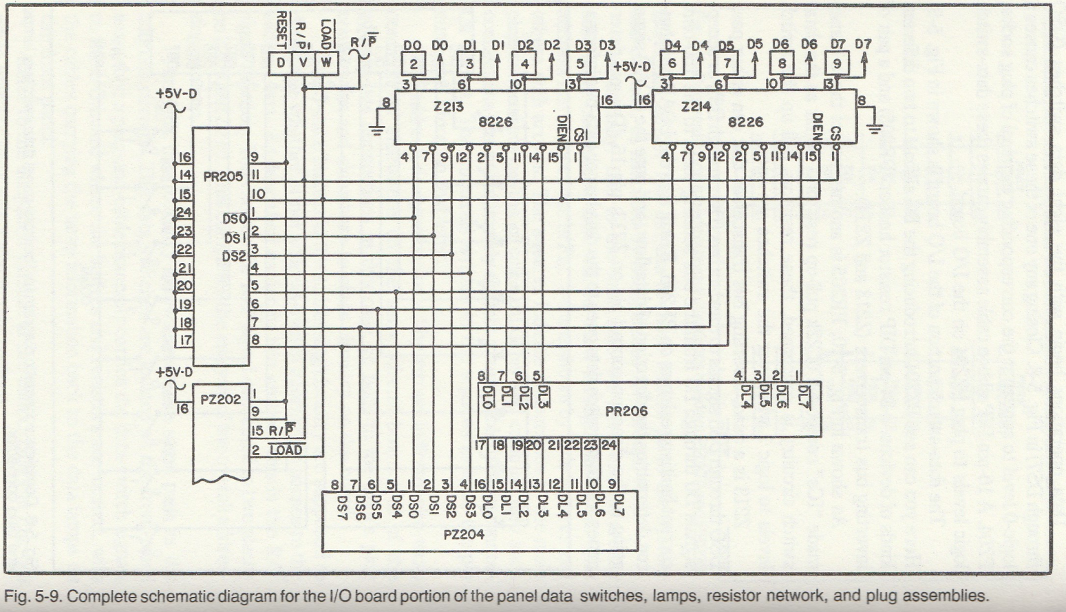
build/5-front-panel/images/fig.5-9.png
