cartheur/aiventure-rodney/build/5-front-panel/images/fig.5-13.png

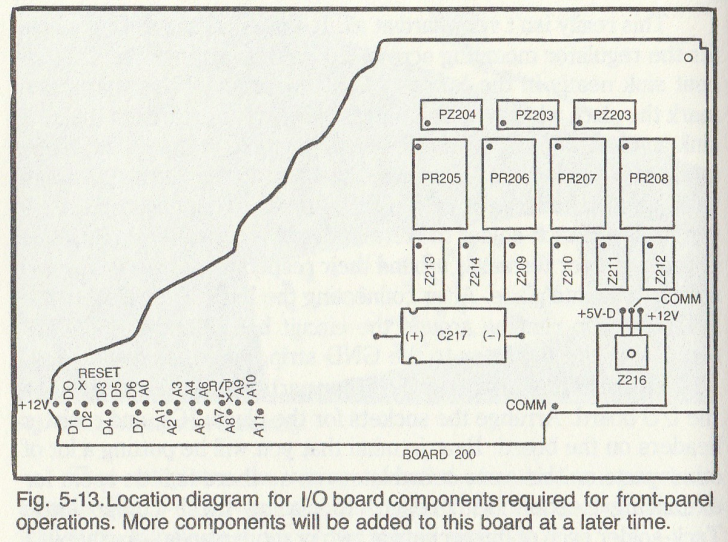
build/5-front-panel/images/fig.5-13.png
