cartheur/aiventure-rodney/build/5-front-panel/images/io-panel-colors-logic.png

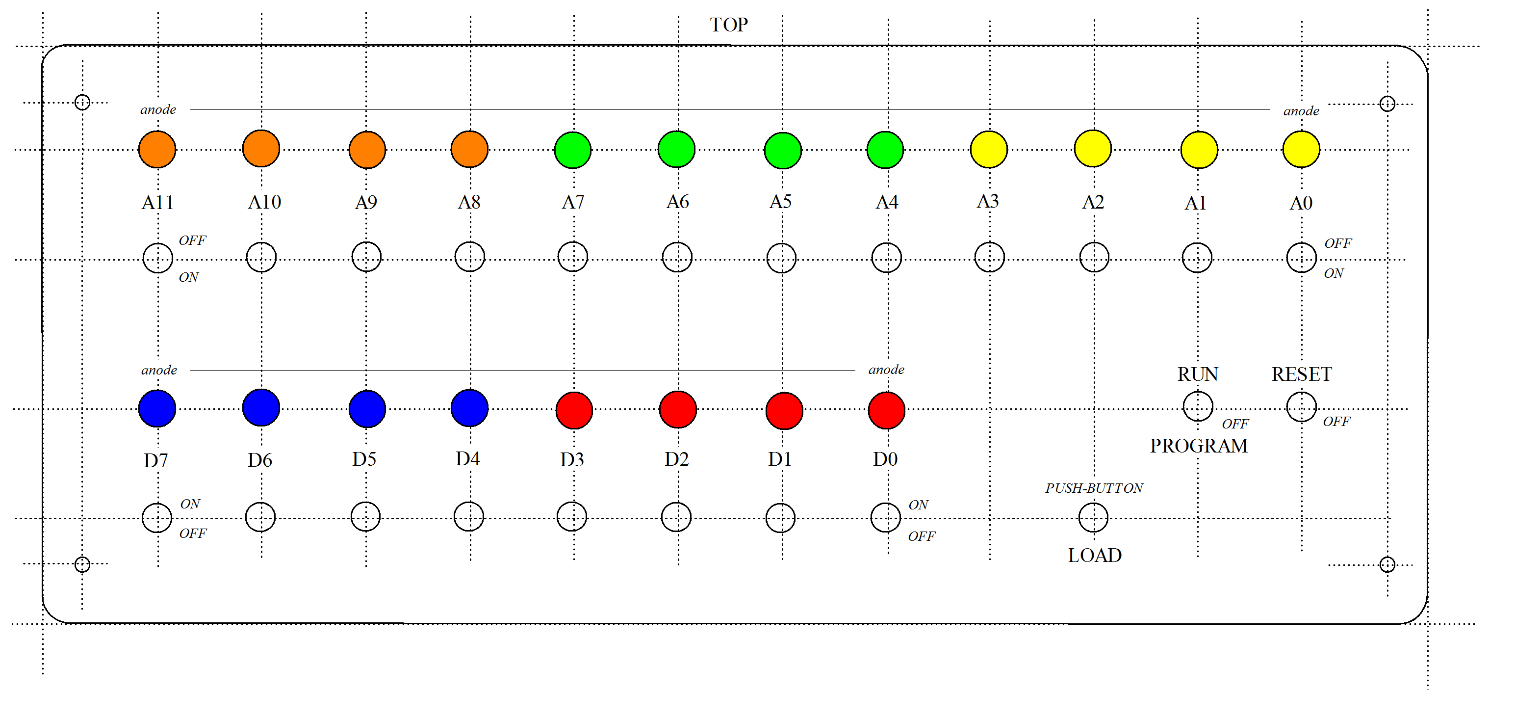
build/5-front-panel/images/io-panel-colors-logic.png
