cartheur/aiventure-rodney/build/5-front-panel/images/table.5-3.png

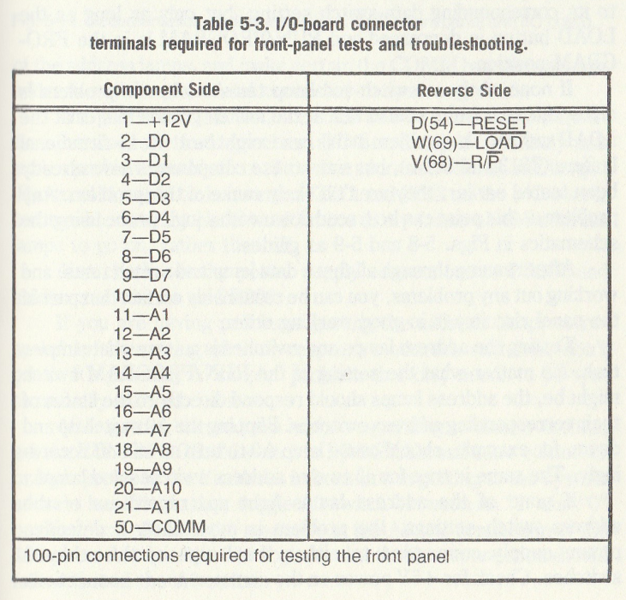
build/5-front-panel/images/table.5-3.png
