cartheur/aiventure-rodney/build/5-front-panel/interface/user-interface-working.png

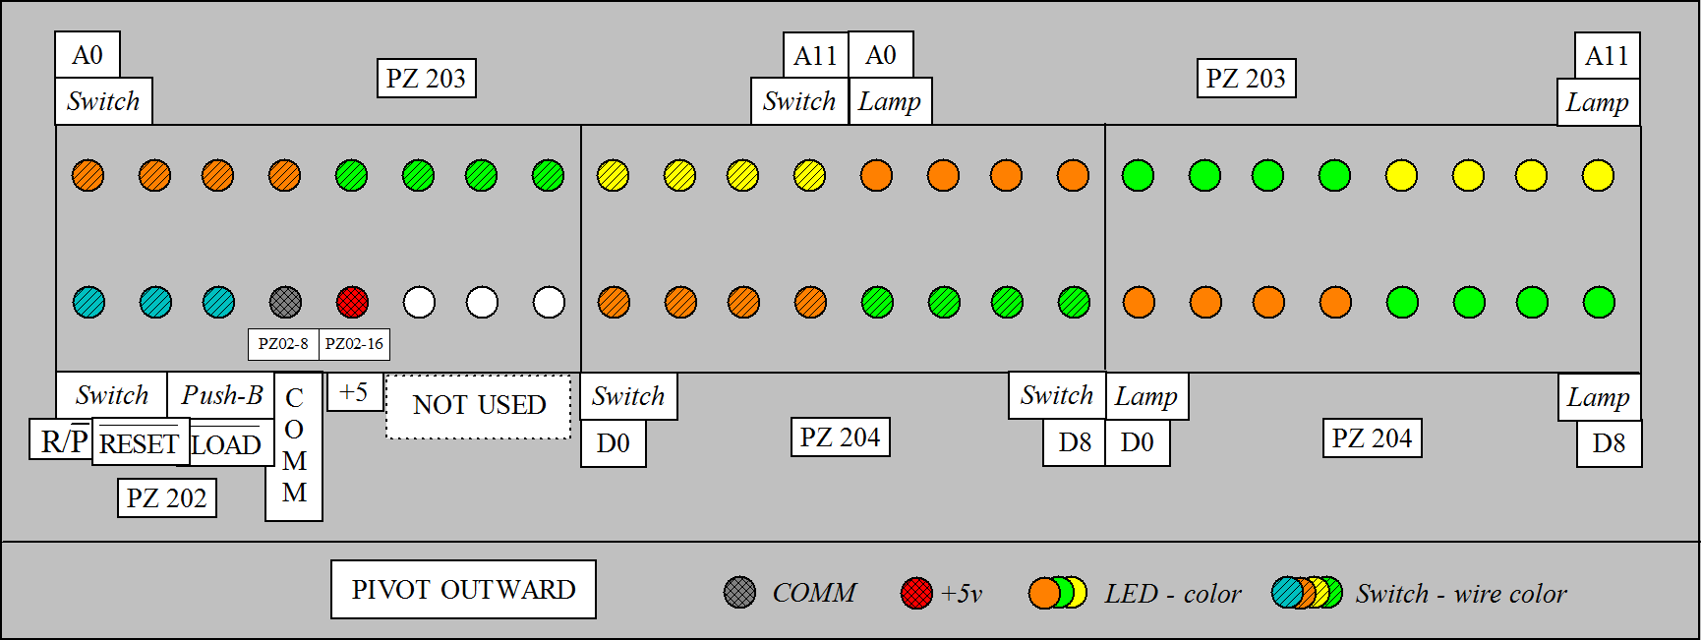
build/5-front-panel/interface/user-interface-working.png
