cartheur/aiventure-rodney/build/6-function-select/images/fig.6-1.png

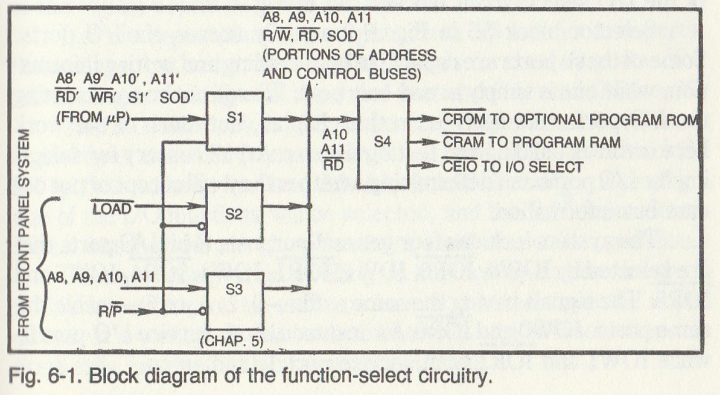
build/6-function-select/images/fig.6-1.png
