cartheur/aiventure-rodney/build/6-function-select/images/table.6-2.png

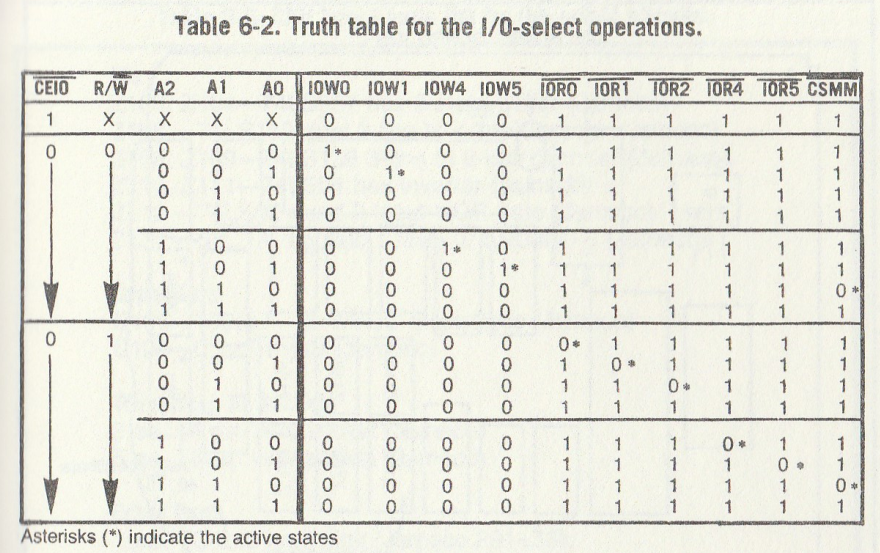
build/6-function-select/images/table.6-2.png
