cartheur/aiventure-rodney/build/6-function-select/images/table.6-4.png

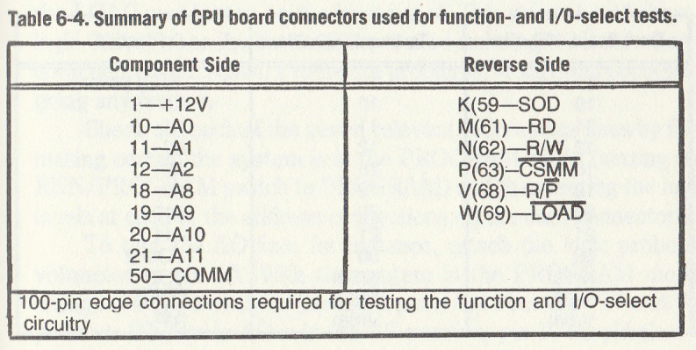
build/6-function-select/images/table.6-4.png
