cartheur/aiventure-rodney/build/6-function-select/images/table.6-5.png

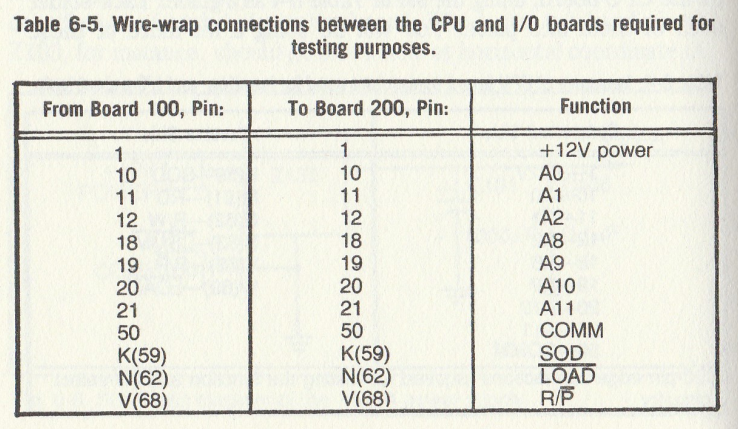
build/6-function-select/images/table.6-5.png
