cartheur/aiventure-rodney/build/7-ram-ports/images/fig.7-1.png

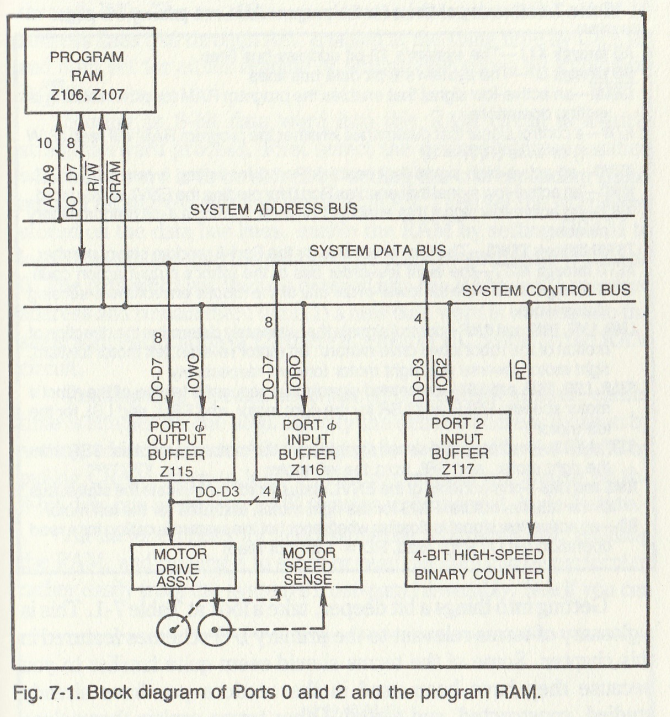
build/7-ram-ports/images/fig.7-1.png
