cartheur/aiventure-rodney/build/7-ram-ports/images/fig.7-2.png

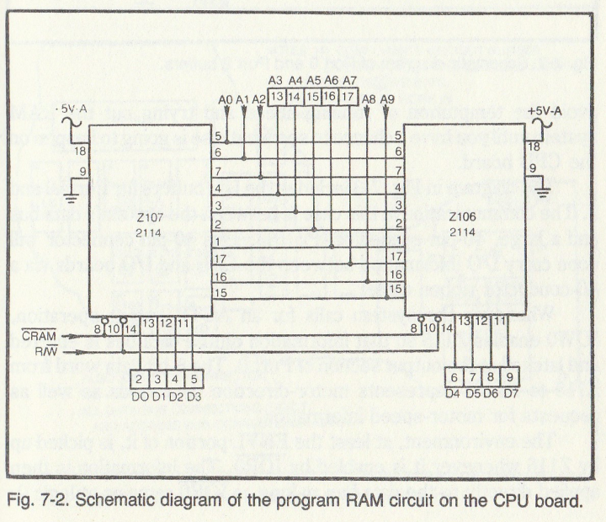
build/7-ram-ports/images/fig.7-2.png
