cartheur/aiventure-rodney/build/7-ram-ports/images/fig.7-4.png

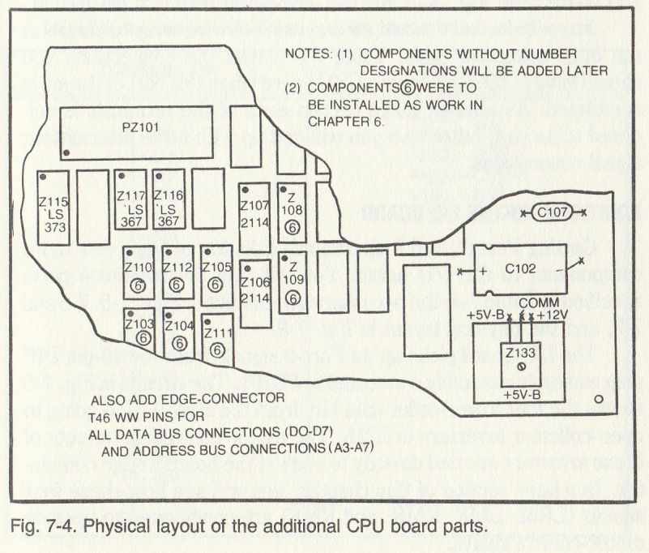
build/7-ram-ports/images/fig.7-4.png
