cartheur/aiventure-rodney/build/7-ram-ports/images/fig.7-7.png

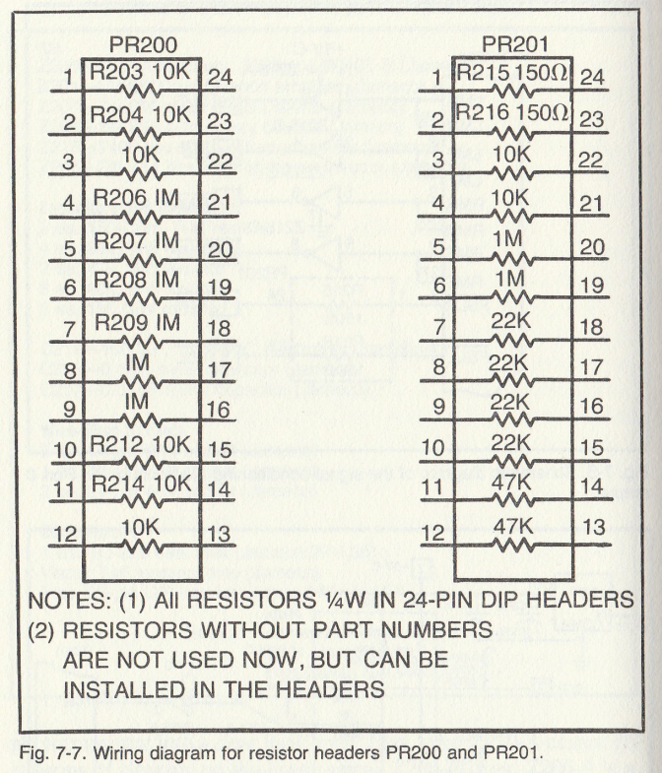
build/7-ram-ports/images/fig.7-7.png
