cartheur/aiventure-rodney/build/7-ram-ports/images/fig.7-8.png

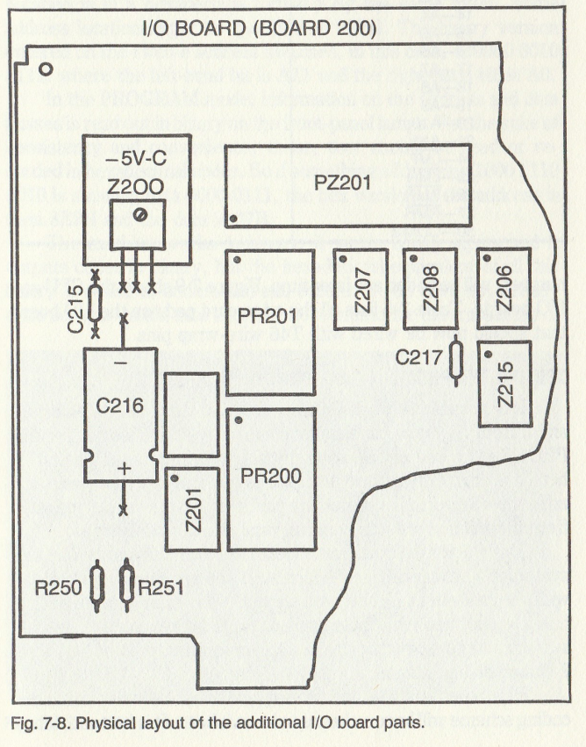
build/7-ram-ports/images/fig.7-8.png
