cartheur/aiventure-rodney/build/7-ram-ports/images/table.7-1.png

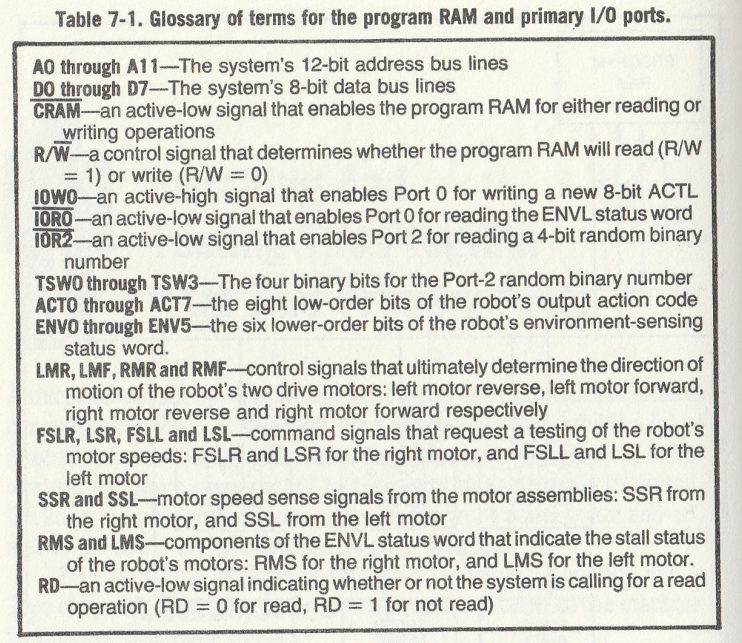
build/7-ram-ports/images/table.7-1.png
