cartheur/aiventure-rodney/build/7-ram-ports/images/table.7-5.png

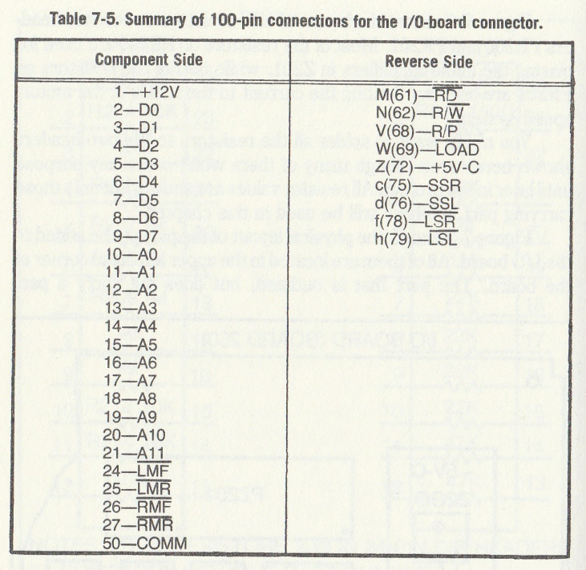
build/7-ram-ports/images/table.7-5.png
