cartheur/aiventure-rodney/build/7-ram-ports/images/table.7-6.png

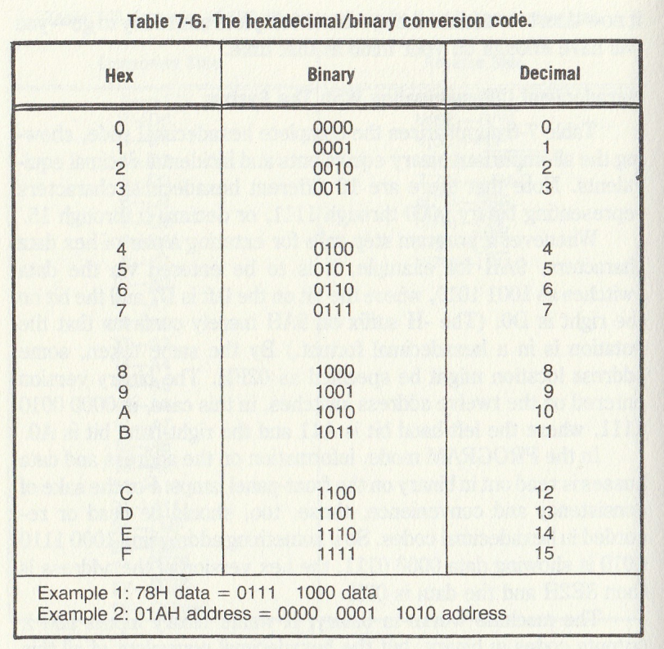
build/7-ram-ports/images/table.7-6.png
