cartheur/aiventure-rodney/diagrams/RodneyBoardA.pdf

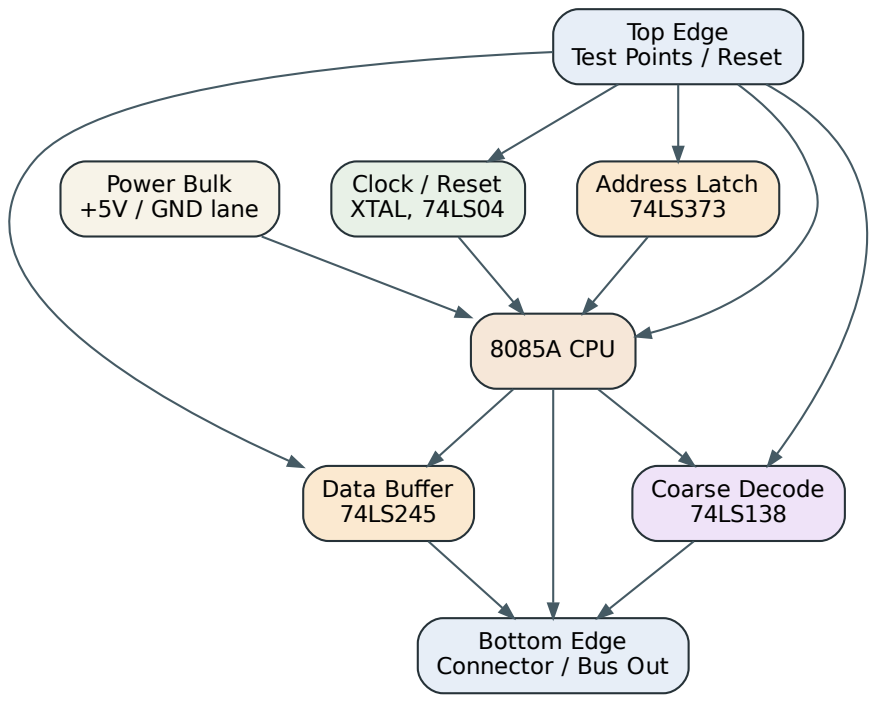
[picture p125: page 1]
Clock / Reset XTAL, 74LS04; Address Latch 74LS373; 8085A CPU; Data Buffer 74LS245; Coarse Decode 74LS138; Power Bulk +5V / GND lane

Top Edge
Test Points / Reset

Bottom Edge
Connector / Bus Out
