cartheur/aiventure-rodney/diagrams/RodneyBoardB.pdf

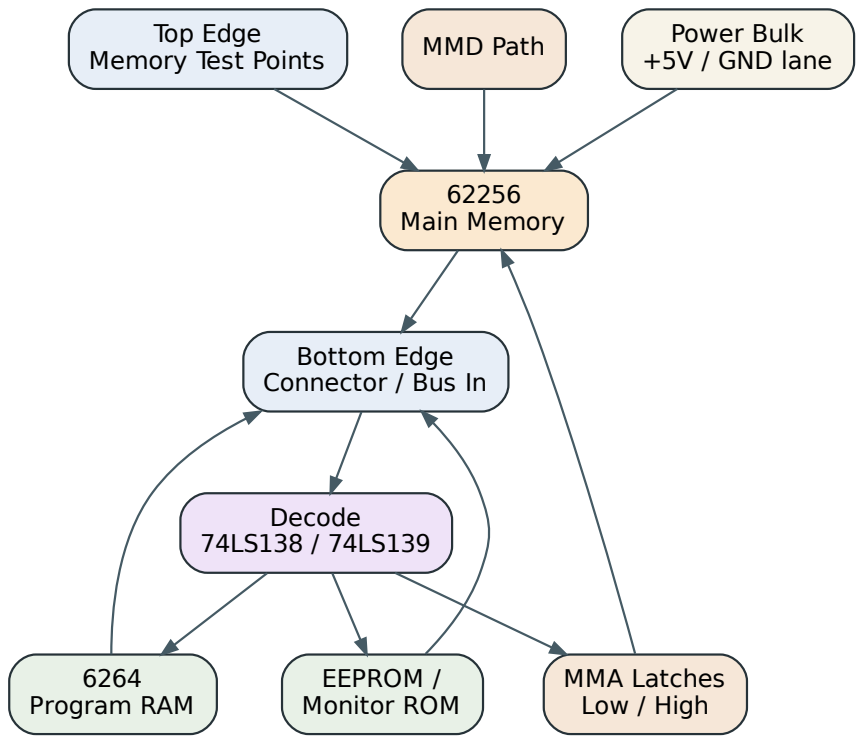
[picture p126: page 1]
62256 Main Memory; Decode 74LS138 / 74LS139; MMA Latches Low / High; 6264 Program RAM; EEPROM / Monitor ROM; MMD Path; Power Bulk; +5V / GND lane

Top Edge
Memory Test Points

Bottom Edge
Connector / Bus In
