cartheur/aiventure-rodney/diagrams/RodneyBoardC.pdf

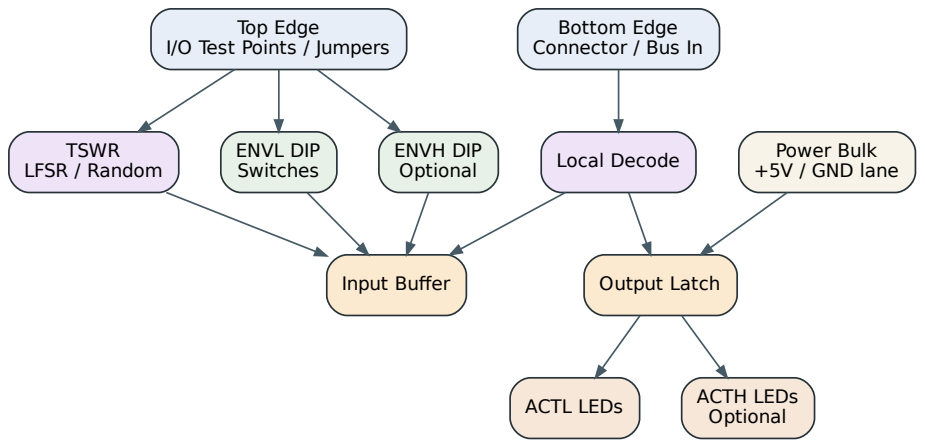
[picture p127: page 1]
Top Edge; TSWR LFSR / Random; ENVL DIP Switches; ENVH DIP Optional; Input Buffer; Output Latch; ACTL LEDs; ACTH LEDs; Optional; Local Decode; Power Bulk; +5V / GND lane

Bottom Edge
Connector / Bus In

I/O Test Points / Jumpers
