cartheur/aiventure-rodney/diagrams/EmbodiedBehaviors.pdf

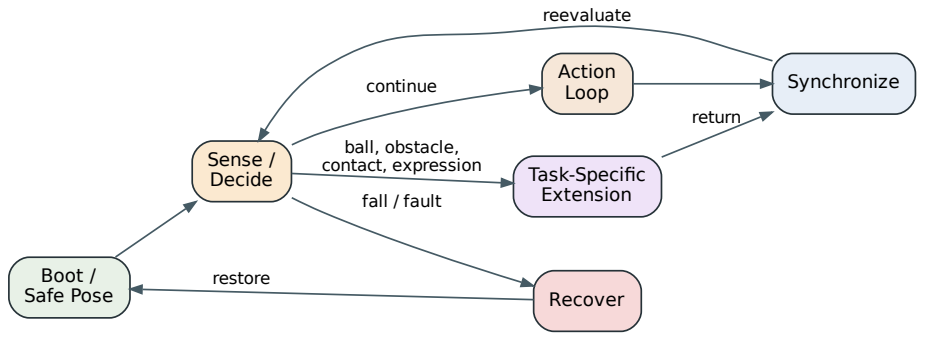
[picture p137: page 1]
Boot / Safe Pose; Sense / Decide; Action Loop continue; Recover; fall / fault; Task-Specific Extension; ball, obstacle, contact, expression; Synchronize; reevaluate; restore; return
