cartheur/aiventure-rodney/self-programming/trainer/kicad/8085_trainer.kicad_sch

## KiCad design self-programming/trainer/kicad/8085_trainer.kicad_sch (2025-05-20)

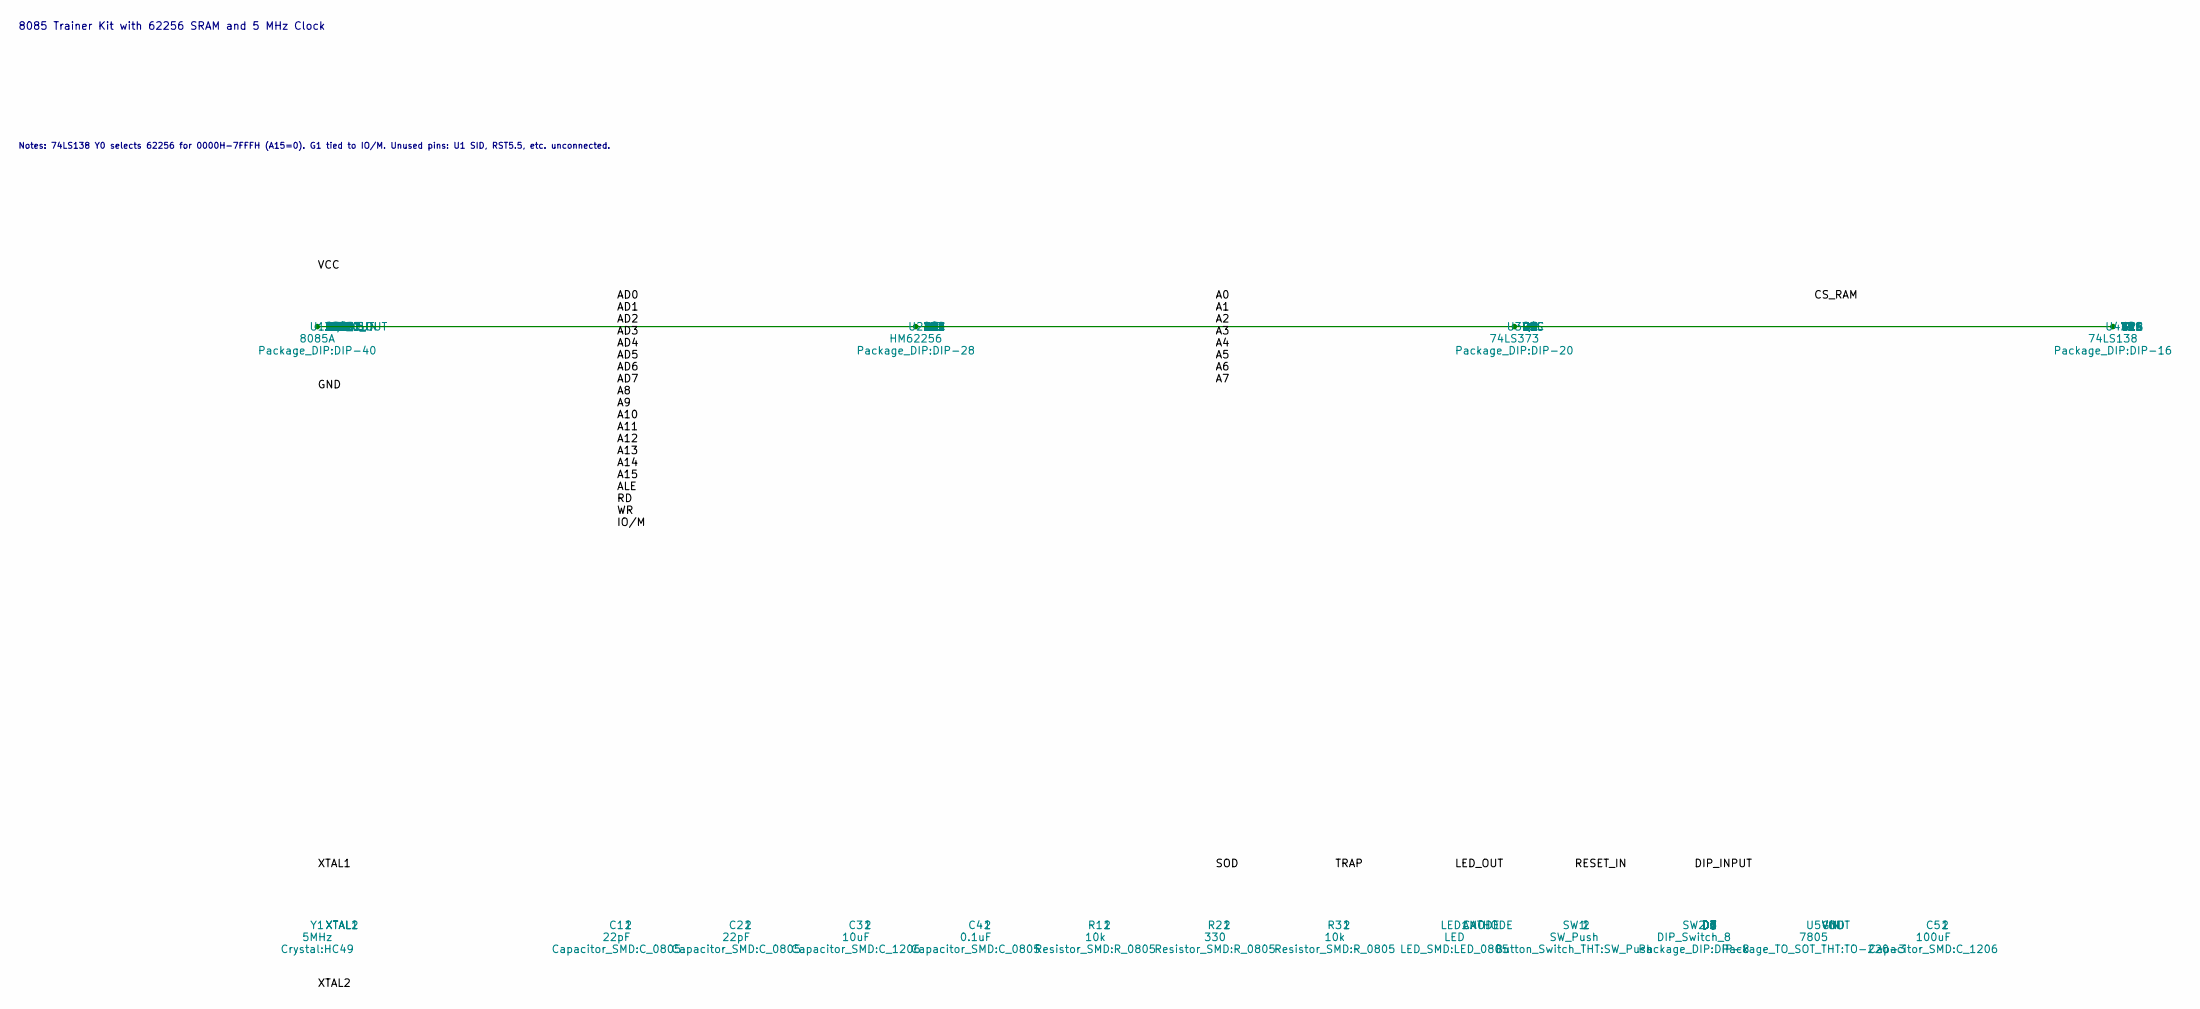
[picture p140: schematic 8085_trainer.kicad_sch]

Parts:
C1, C2: 22pF; C_0805
C3: 10uF; C_1206
C4: 0.1uF; C_0805
C5: 100uF; C_1206
LED1: LED; LED_0805
R1, R3: 10k; R_0805
R2: 330; R_0805
SW1: SW_Push
SW2: DIP_Switch_8; DIP-8
U1: 8085A; DIP-40
U2: HM62256; DIP-28
U3: 74LS373; DIP-20
U4: 74LS138; DIP-16
U5: 7805; TO-220-3
Y1: 5MHz; HC49

Connections:
unnamed: U1., U2., U3., U4.

Notes on the sheet:
8085 Trainer Kit with 62256 SRAM and 5 MHz Clock
Notes: 74LS138 Y0 selects 62256 for 0000H-7FFFH (A15=0). G1 tied to IO/M. Unused pins: U1 SID, RST5.5, etc. unconnected.
